mattmcwru/MPCNC-Build/Printed_Parts/MPCNC_Harbor_Fright_Cutout_Tool_Mount/images/f7ad241b8bc4b4fceb94680d84f262ed_preview_featured.jpg

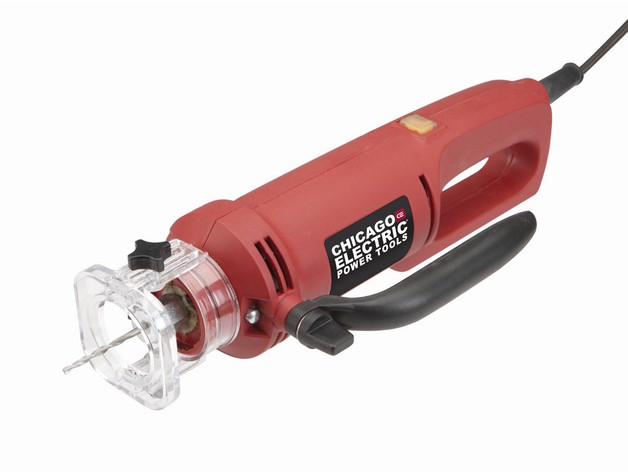
Printed_Parts/MPCNC_Harbor_Fright_Cutout_Tool_Mount/images/f7ad241b8bc4b4fceb94680d84f262ed_preview_featured.jpg
