mattmcwru/MPCNC-Build/Printed_Parts/MPCNC_Belt_Mount_Tensioner/images/5b18fd9a31a962e26c91805c583ef1f9_preview_featured.jpg

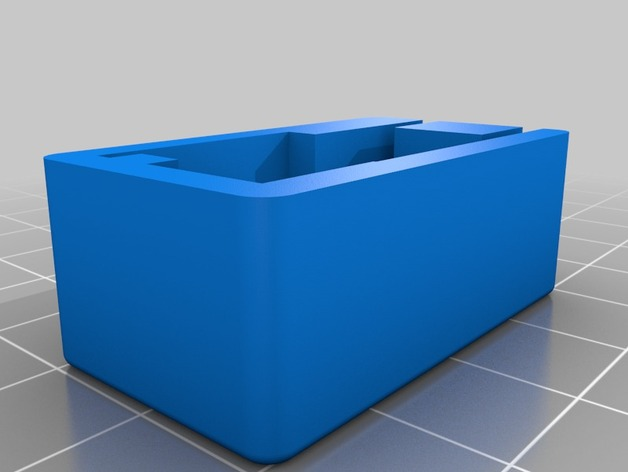
Printed_Parts/MPCNC_Belt_Mount_Tensioner/images/5b18fd9a31a962e26c91805c583ef1f9_preview_featured.jpg
