mattmcwru/MPCNC-Build/Printed_Parts/MPCNC_Belt_Mount_Tensioner/images/118bb4b1bc5640f76486a74081724c0c_preview_featured.jpg

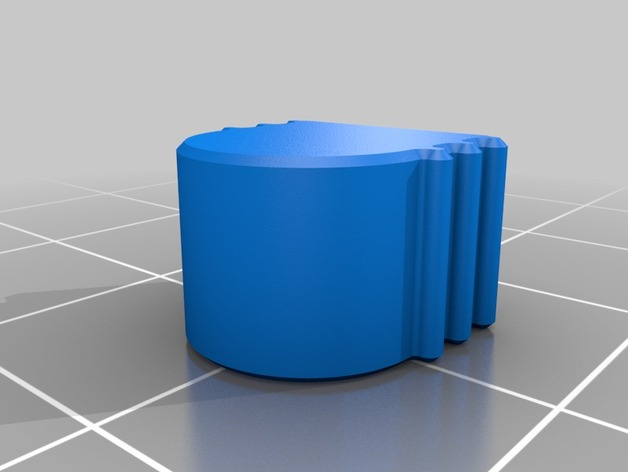
Printed_Parts/MPCNC_Belt_Mount_Tensioner/images/118bb4b1bc5640f76486a74081724c0c_preview_featured.jpg
