mattmcwru/MPCNC-Build/Printed_Parts/MPCNC_Belt_Mount_Tensioner/images/0129aa42869a3df930a46816420d5308_preview_featured.jpg

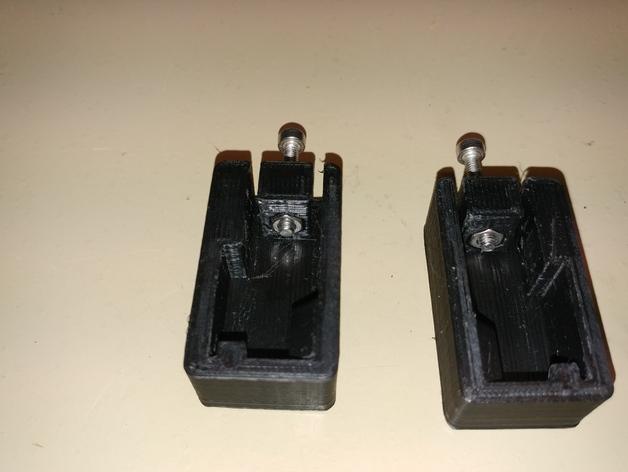
Printed_Parts/MPCNC_Belt_Mount_Tensioner/images/0129aa42869a3df930a46816420d5308_preview_featured.jpg
