mattmcwru/MPCNC-Build/Printed_Parts/MPCNC_Belt_Mount_Tensioner/images/a4fcf2e1120b8b7a6934baca6f5d6d2d_preview_featured.jpg

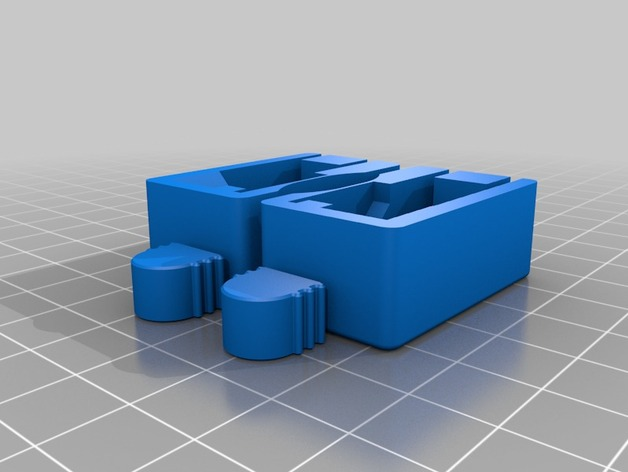
Printed_Parts/MPCNC_Belt_Mount_Tensioner/images/a4fcf2e1120b8b7a6934baca6f5d6d2d_preview_featured.jpg
