mattmcwru/MPCNC-Build/Printed_Parts/MPCNC_Belt_Mount_Tensioner/images/a68c1adb7a9085717290787e775d51c3_preview_featured.jpg

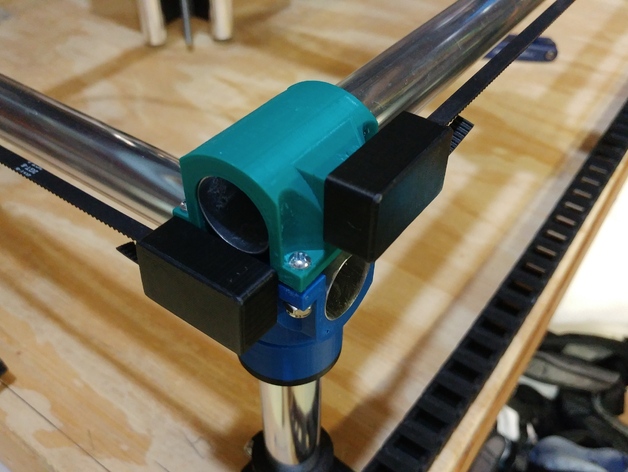
Printed_Parts/MPCNC_Belt_Mount_Tensioner/images/a68c1adb7a9085717290787e775d51c3_preview_featured.jpg
