mattmcwru/MPCNC-Build/Printed_Parts/MPCNC_Belt_Mount_Tensioner/images/b05523cd2e82c112d31e00afcdd35d0d_preview_featured.jpg

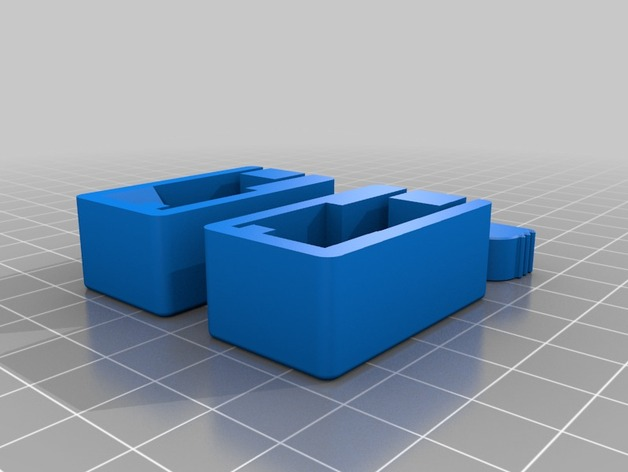
Printed_Parts/MPCNC_Belt_Mount_Tensioner/images/b05523cd2e82c112d31e00afcdd35d0d_preview_featured.jpg
