mattmcwru/MPCNC-Build/Printed_Parts/MPCNC_Belt_Mount_Tensioner/images/c8c6ffc99c06a0f2dce8c60c747f504d_preview_featured.jpg

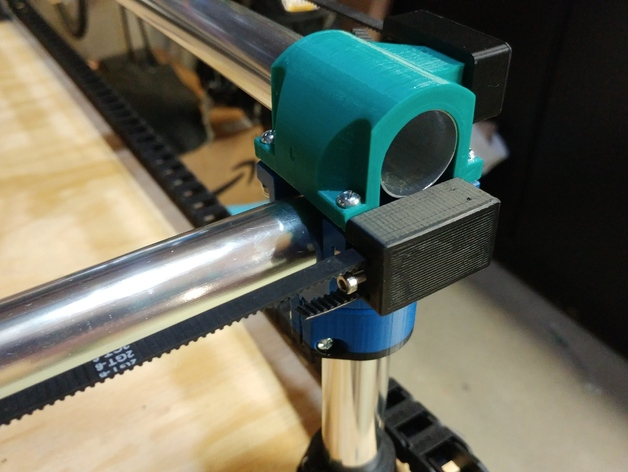
Printed_Parts/MPCNC_Belt_Mount_Tensioner/images/c8c6ffc99c06a0f2dce8c60c747f504d_preview_featured.jpg
