mattmcwru/MPCNC-Build/Printed_Parts/MPCNC_Belt_Mount_Tensioner/images/f6a336b1bc5efcc05f3e396646c9c925_preview_featured.jpg

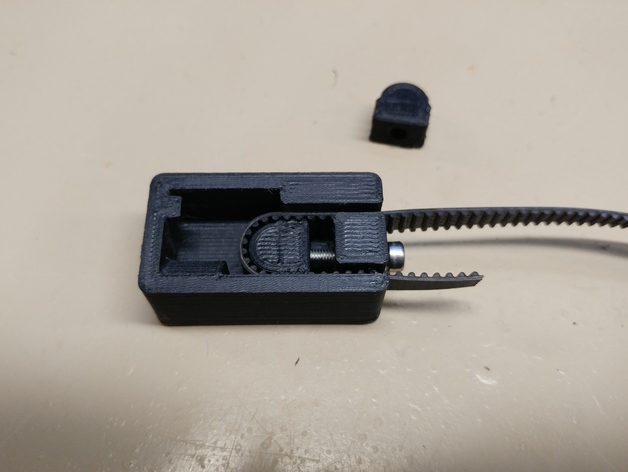
Printed_Parts/MPCNC_Belt_Mount_Tensioner/images/f6a336b1bc5efcc05f3e396646c9c925_preview_featured.jpg
