mattmcwru/MPCNC-Build/Printed_Parts/MPCNC_Dual_Endstop_Plates/images/4f32e94896d080e1614057bec8d3dcbc_preview_featured.jpg

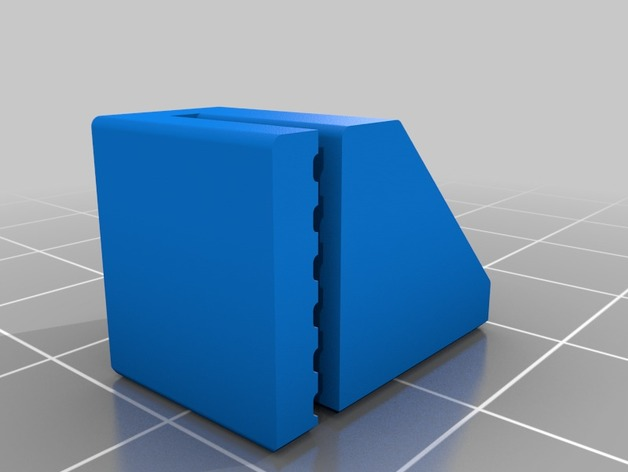
Printed_Parts/MPCNC_Dual_Endstop_Plates/images/4f32e94896d080e1614057bec8d3dcbc_preview_featured.jpg
