mattmcwru/MPCNC-Build/Printed_Parts/MPCNC_Dual_Endstop_Plates/images/6a49a4de091cbfa820c69511d2fc30e3_preview_featured.jpg

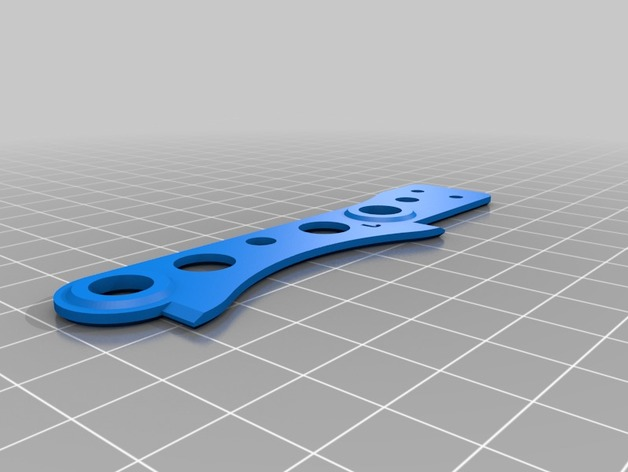
Printed_Parts/MPCNC_Dual_Endstop_Plates/images/6a49a4de091cbfa820c69511d2fc30e3_preview_featured.jpg
