mattmcwru/MPCNC-Build/Printed_Parts/MPCNC_Dual_Endstop_Plates/images/8cfda778197d712c990b11f8b45d0fdf_preview_featured.jpg

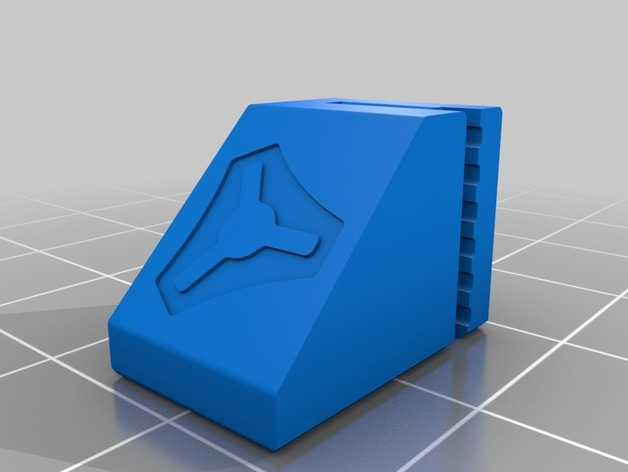
Printed_Parts/MPCNC_Dual_Endstop_Plates/images/8cfda778197d712c990b11f8b45d0fdf_preview_featured.jpg
