mattmcwru/MPCNC-Build/Printed_Parts/MPCNC_Dual_Endstop_Plates/images/de4bcbbb7ce7ebc580b4e3beed8e2b2a_preview_featured.jpg

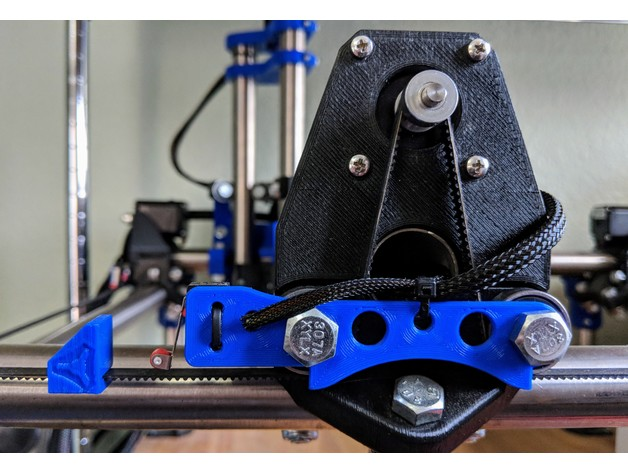
Printed_Parts/MPCNC_Dual_Endstop_Plates/images/de4bcbbb7ce7ebc580b4e3beed8e2b2a_preview_featured.jpg
