mattmcwru/MPCNC-Build/Printed_Parts/MPCNC_Harbor_Fright_Cutout_Tool_Mount/images/6a102007f02f2ae56196f1c2347e11f0_preview_featured.jpg

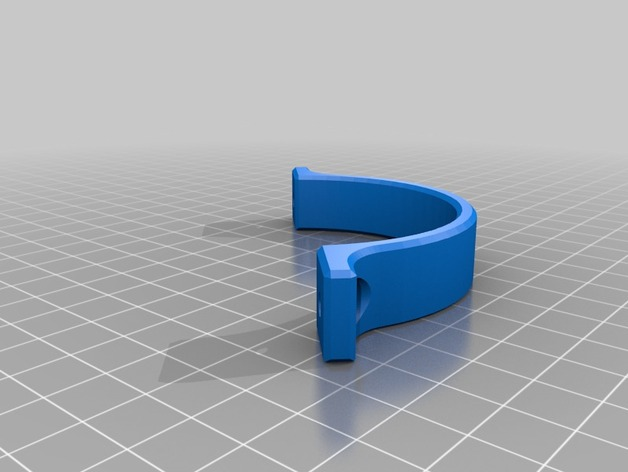
Printed_Parts/MPCNC_Harbor_Fright_Cutout_Tool_Mount/images/6a102007f02f2ae56196f1c2347e11f0_preview_featured.jpg
