mattmcwru/MPCNC-Build/Printed_Parts/MPCNC_Harbor_Fright_Cutout_Tool_Mount/images/9f360c5ab7736510df54c882e9dbf188_preview_featured.jpeg

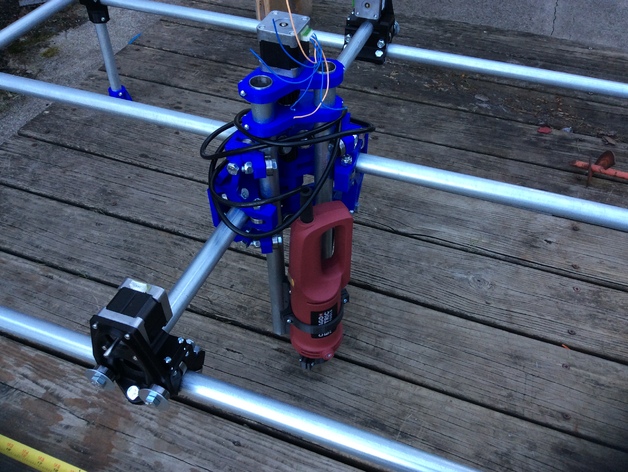
Printed_Parts/MPCNC_Harbor_Fright_Cutout_Tool_Mount/images/9f360c5ab7736510df54c882e9dbf188_preview_featured.jpeg
