mattmcwru/MPCNC-Build/Printed_Parts/MPCNC_Harbor_Fright_Cutout_Tool_Mount/images/031cdfd2edde983c23e4769dfbf6b3be_preview_featured.jpg

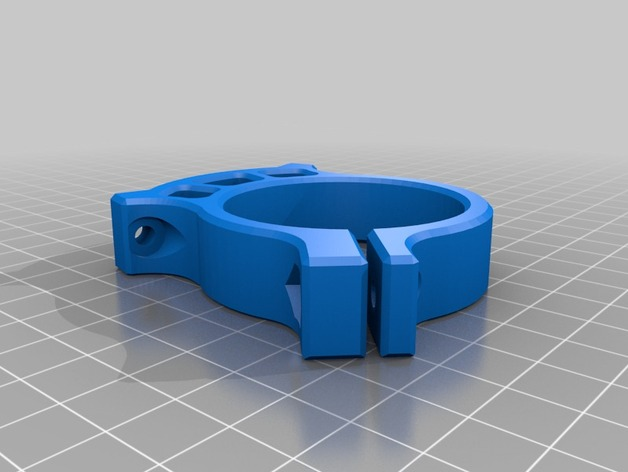
Printed_Parts/MPCNC_Harbor_Fright_Cutout_Tool_Mount/images/031cdfd2edde983c23e4769dfbf6b3be_preview_featured.jpg
