mattmcwru/MPCNC-Build/Printed_Parts/MPCNC_Harbor_Fright_Cutout_Tool_Mount/images/af0f49f9789b260aa54c982aef7ff063_preview_featured.jpg

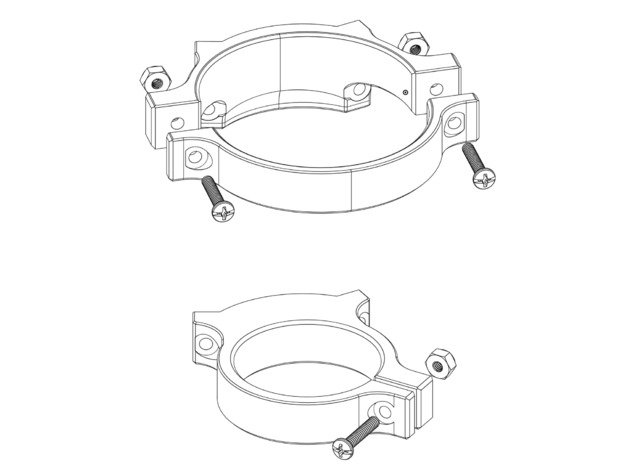
Printed_Parts/MPCNC_Harbor_Fright_Cutout_Tool_Mount/images/af0f49f9789b260aa54c982aef7ff063_preview_featured.jpg
