mattmcwru/MPCNC-Build/Printed_Parts/MPCNC_Harbor_Fright_Cutout_Tool_Mount/images/c593cc7923c47d9a5d14d5e01f252088_preview_featured.jpg

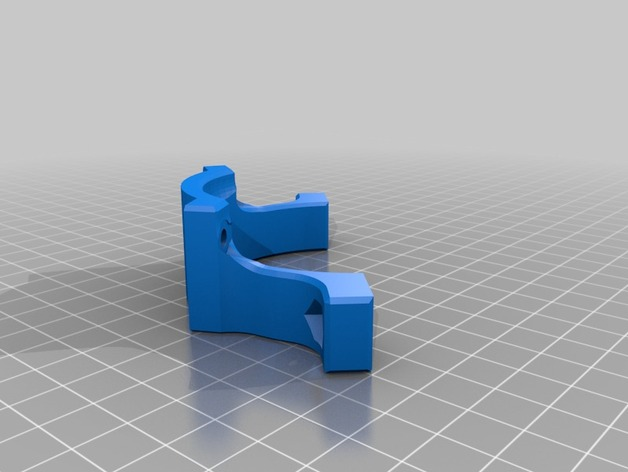
Printed_Parts/MPCNC_Harbor_Fright_Cutout_Tool_Mount/images/c593cc7923c47d9a5d14d5e01f252088_preview_featured.jpg
