mattmcwru/MPCNC-Build/Printed_Parts/MPCNC_Harbor_Fright_Cutout_Tool_Mount/images/d2b5ca33bd970f64a6301fa75ae2eb22_preview_featured.jpg

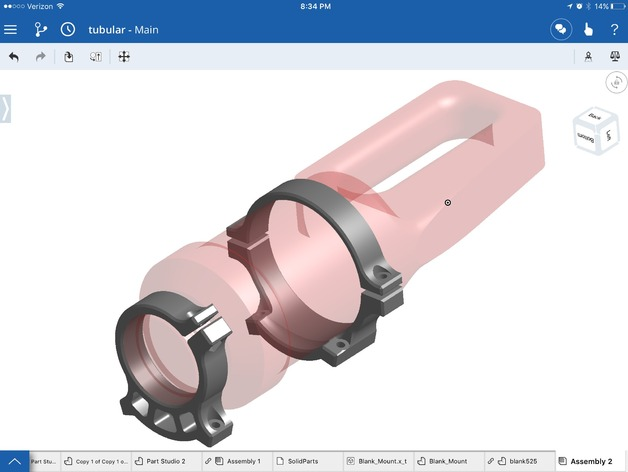
Printed_Parts/MPCNC_Harbor_Fright_Cutout_Tool_Mount/images/d2b5ca33bd970f64a6301fa75ae2eb22_preview_featured.jpg
