mattmcwru/MPCNC-Build/Printed_Parts/MPCNC_Pen_Holder/images/3a7e917523091c81a72ba8f813cce41a_preview_featured.jpg

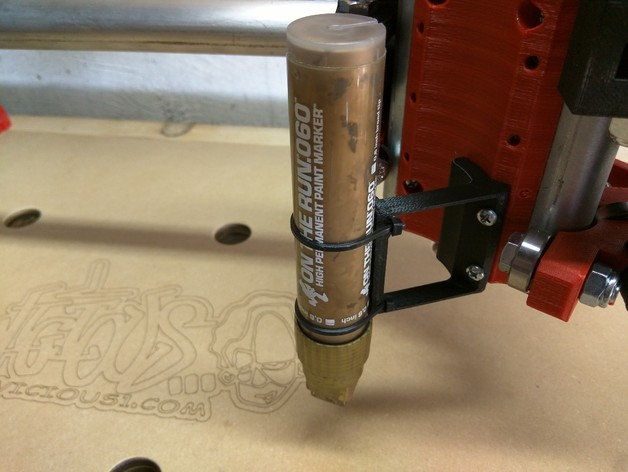
Printed_Parts/MPCNC_Pen_Holder/images/3a7e917523091c81a72ba8f813cce41a_preview_featured.jpg
