mattmcwru/MPCNC-Build/Printed_Parts/MPCNC_Pen_Holder/images/4c0c8f3b025ac8f8c0729633aa5849b6_preview_featured.jpg

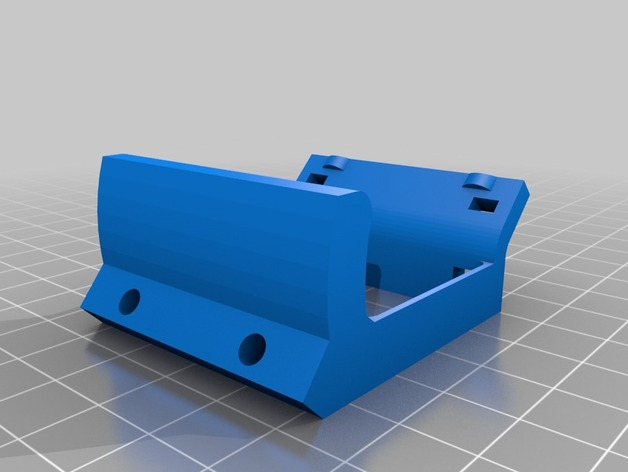
Printed_Parts/MPCNC_Pen_Holder/images/4c0c8f3b025ac8f8c0729633aa5849b6_preview_featured.jpg
