mattmcwru/MPCNC-Build/Printed_Parts/MPCNC_Pen_Holder/images/76b8588e2262610db6ddbcaa5a4f088d_preview_featured.jpg

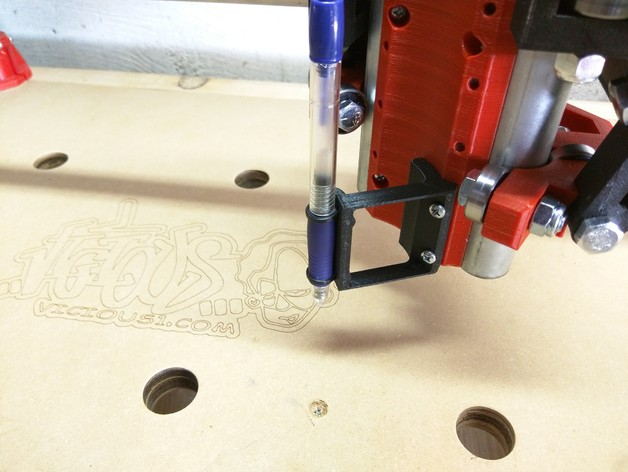
Printed_Parts/MPCNC_Pen_Holder/images/76b8588e2262610db6ddbcaa5a4f088d_preview_featured.jpg
