mattmcwru/MPCNC-Build/Printed_Parts/MPCNC_Pen_Holder/images/da3b15e401a95bbbfccdcf46860e9864_preview_featured.jpg

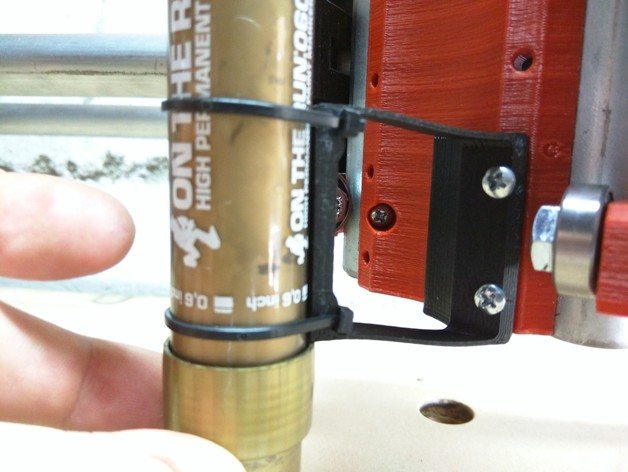
Printed_Parts/MPCNC_Pen_Holder/images/da3b15e401a95bbbfccdcf46860e9864_preview_featured.jpg
