mattmcwru/MPCNC-Build/Printed_Parts/MPCNC_Pipe_Caps/MPCNC_Pipe_Caps v2.png

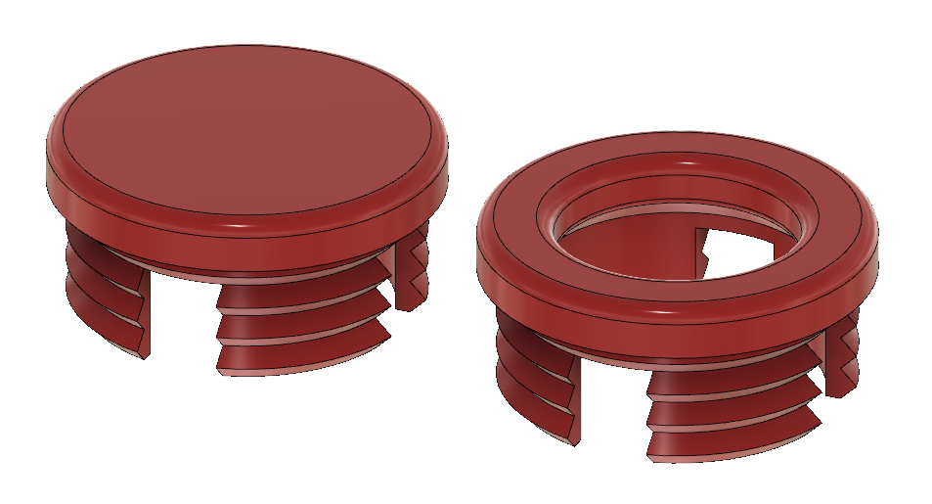
Printed_Parts/MPCNC_Pipe_Caps/MPCNC_Pipe_Caps v2.png
