mattmcwru/MPCNC-Build/Printed_Parts/MPCNC_TapeWireGuide/umc_projects/UM2_TapeWireGuideZMount_v3.3mf

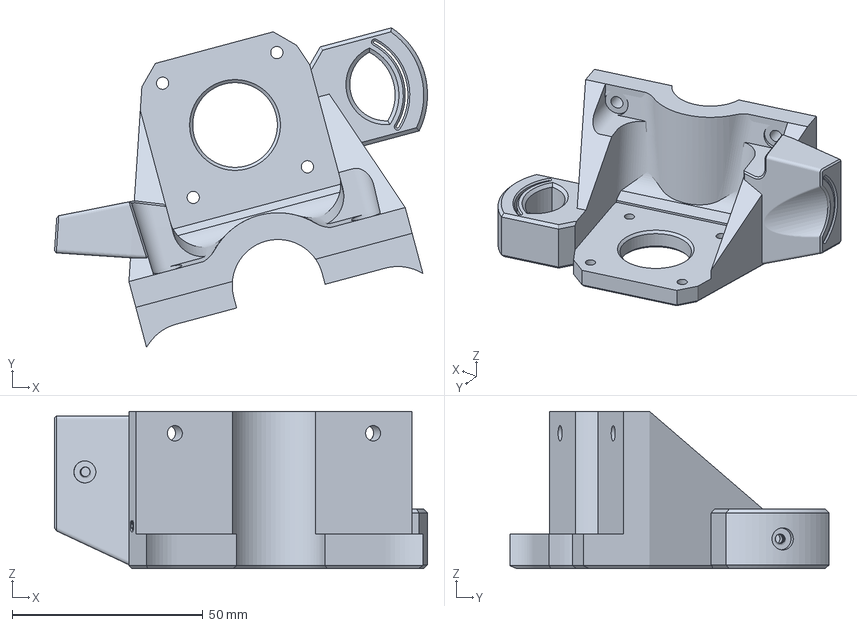
[picture p40: CAD file, 2019-02-07]
Printed_Parts/MPCNC_TapeWireGuide/umc_projects/UM2_TapeWireGuideZMount_v3.3mf
97.8 x 83.7 x 41.2 mm
