mattmcwru/MPCNC-Build/Printed_Parts/MPCNC_Belt_Mount_Tensioner/files/Belt_Anchor_Block_v2.1.stl

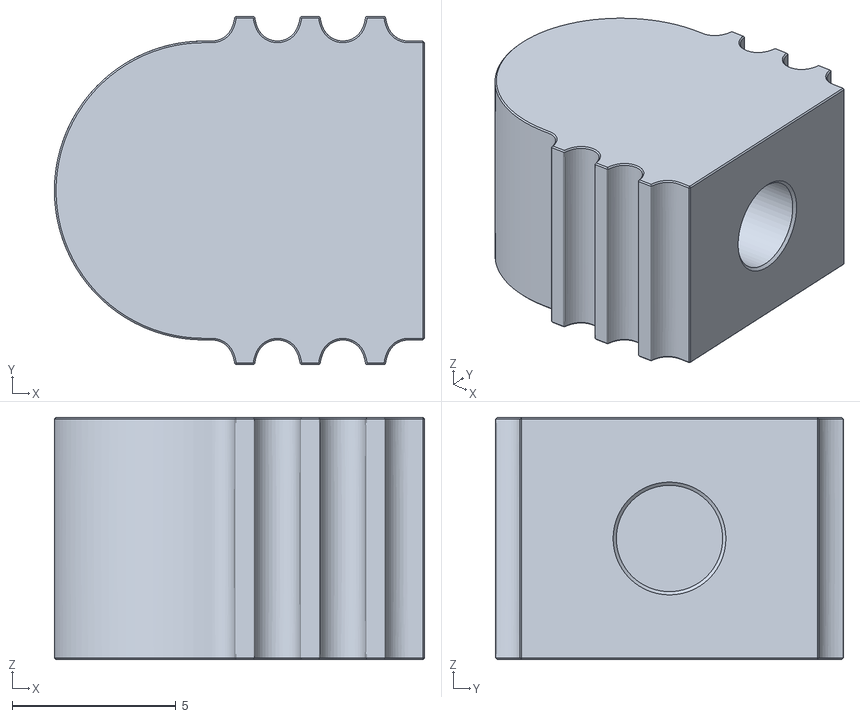
[picture p41: CAD file, 2019-02-19]
Printed_Parts/MPCNC_Belt_Mount_Tensioner/files/Belt_Anchor_Block_v2.1.stl
11.3 x 10.6 x 7.40
