mattmcwru/MPCNC-Build/Printed_Parts/MPCNC_Belt_Mount_Tensioner/umc_projects/UM2_Belt_Anchor_Block_v2.1.3mf

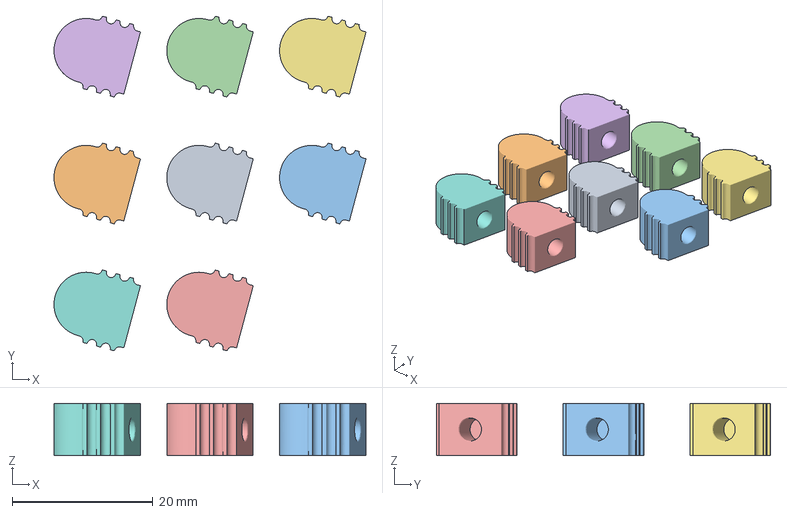
[picture p42: CAD file, 2019-02-19]
Printed_Parts/MPCNC_Belt_Mount_Tensioner/umc_projects/UM2_Belt_Anchor_Block_v2.1.3mf
44.3 x 47.5 x 7.40 mm
