mattmcwru/MPCNC-Build/Printed_Parts/MPCNC_BURLY_C_23p5/files/Lock-CornerC.STL

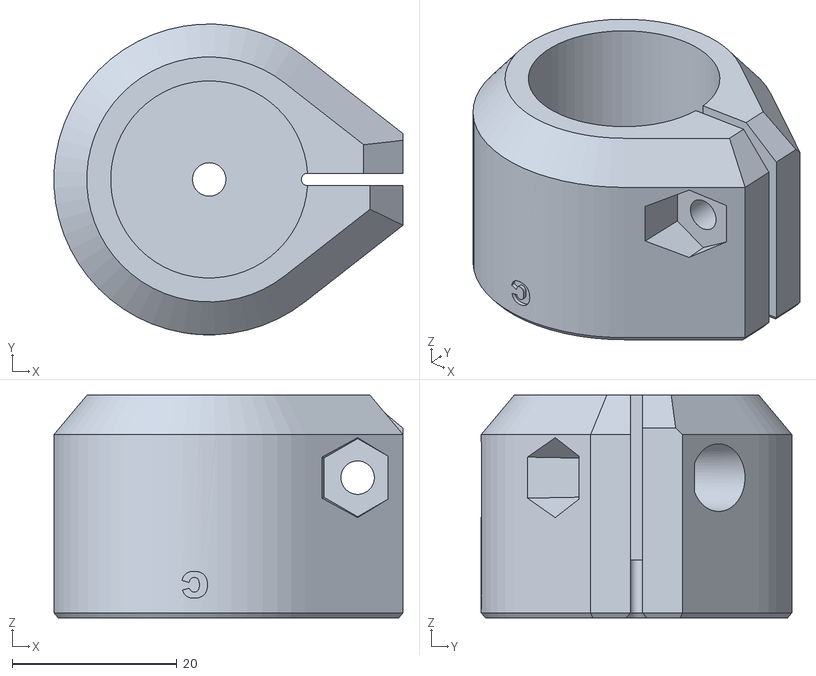
[picture p43: CAD file, 2019-01-15]
Printed_Parts/MPCNC_BURLY_C_23p5/files/Lock-CornerC.STL
42.3 x 37.7 x 27.0
