mattmcwru/MPCNC-Build/Printed_Parts/MPCNC_Dual_Endstop_Plates/files/Stop_Block.STL

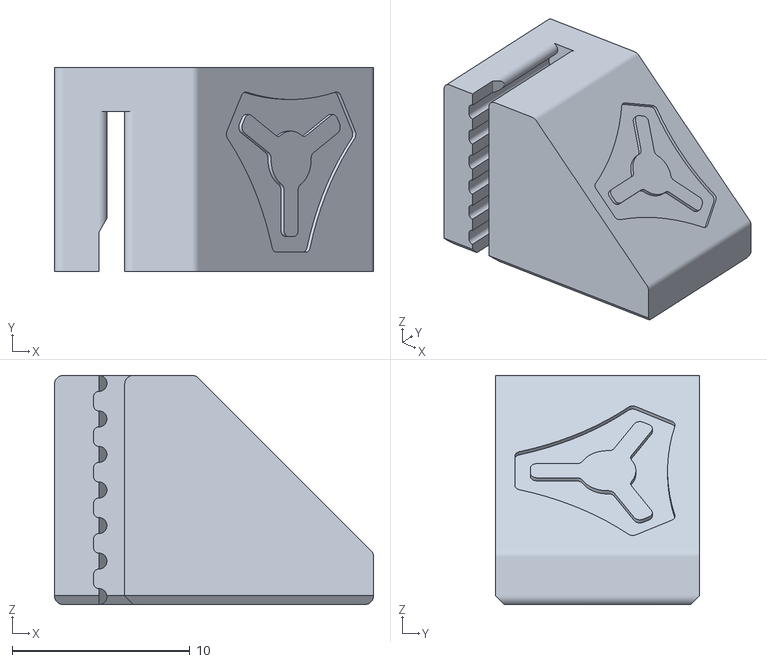
[picture p44: CAD file, 2019-01-26]
Printed_Parts/MPCNC_Dual_Endstop_Plates/files/Stop_Block.STL
17.9 x 11.5 x 12.9
