mattmcwru/MPCNC-Build/Printed_Parts/MPCNC_Dual_Endstop_Plates/umc_projects/UM2_C_Dual_Endstop_RollerPlateM_x2.3mf

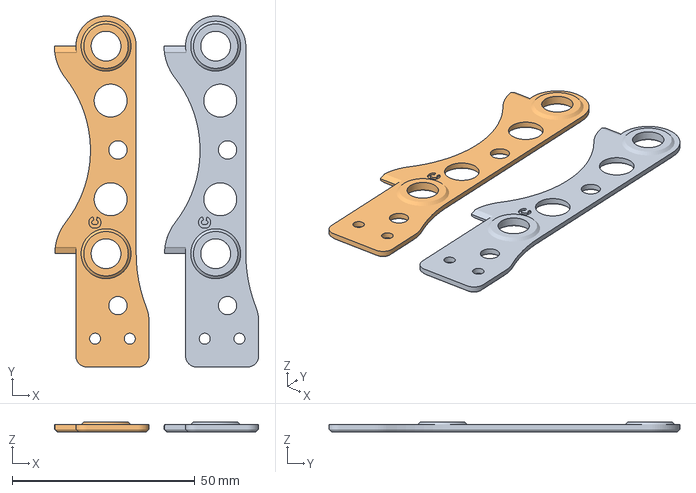
[picture p45: CAD file, 2019-01-29]
Printed_Parts/MPCNC_Dual_Endstop_Plates/umc_projects/UM2_C_Dual_Endstop_RollerPlateM_x2.3mf
55.9 x 96.0 x 2.75 mm
