mattmcwru/MPCNC-Build/Printed_Parts/MPCNC_Harbor_Fright_Cutout_Tool_Mount/files/hf_tool_mount_top.stl

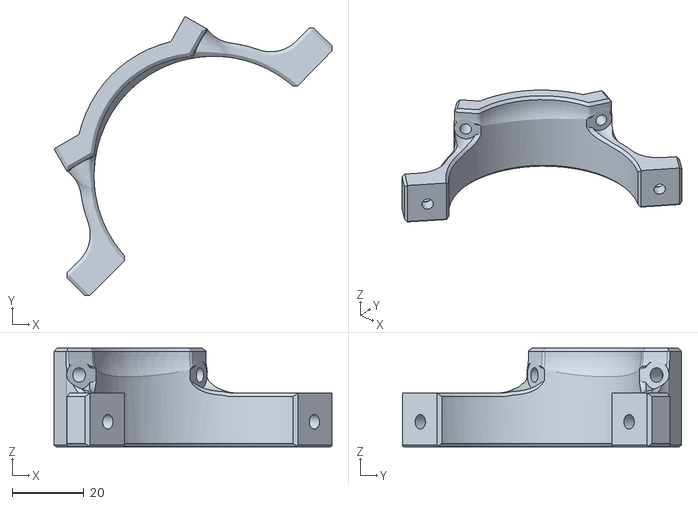
[picture p46: CAD file, 2019-01-15]
Printed_Parts/MPCNC_Harbor_Fright_Cutout_Tool_Mount/files/hf_tool_mount_top.stl
77.3 x 77.5 x 27.5
