mattmcwru/MPCNC-Build/Printed_Parts/MPCNC_Harbor_Fright_Cutout_Tool_Mount/umc-projects/UM2_hf_tool_mount_bottom.3mf

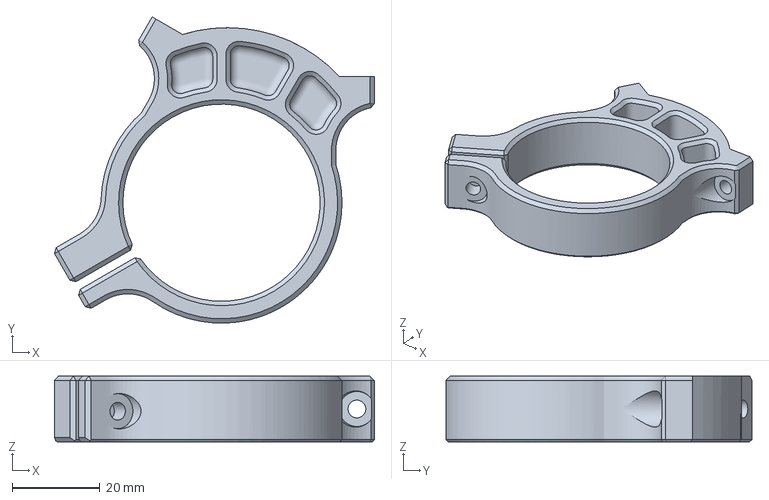
[picture p47: CAD file, 2019-01-15]
Printed_Parts/MPCNC_Harbor_Fright_Cutout_Tool_Mount/umc-projects/UM2_hf_tool_mount_bottom.3mf
73.1 x 69.9 x 15.0 mm
