mattmcwru/MPCNC-Build/Printed_Parts/MPCNC_Pipe_Caps/files/Cap_Open.stl

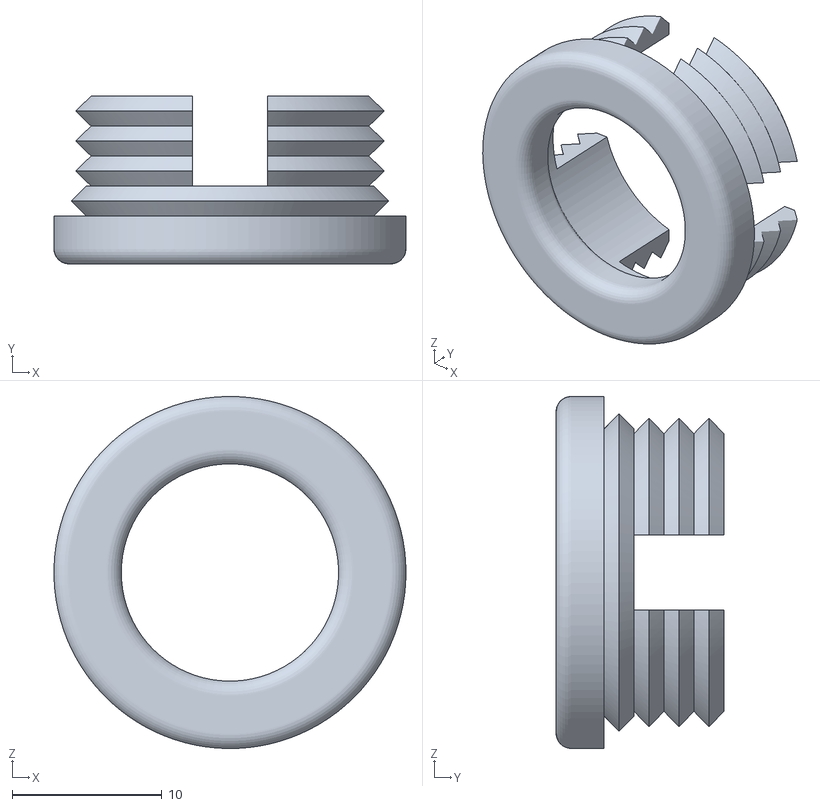
[picture p48: CAD file, 2019-01-27]
Printed_Parts/MPCNC_Pipe_Caps/files/Cap_Open.stl
23.5 x 11.2 x 23.5
