mattmcwru/MPCNC-Build/Printed_Parts/MPCNC_Pipe_Caps/umc_projects/UM2_Caps_6closed_3open.3mf

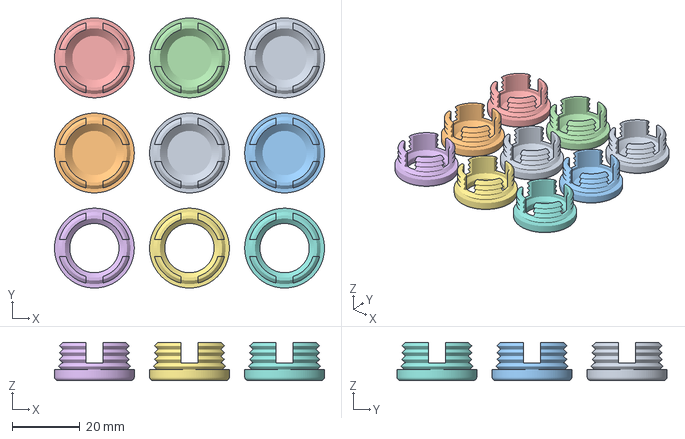
[picture p49: CAD file, 2019-01-29]
Printed_Parts/MPCNC_Pipe_Caps/umc_projects/UM2_Caps_6closed_3open.3mf
79.5 x 79.5 x 11.2 mm
