mattmcwru/MPCNC-Build/Printed_Parts/MPCNC_TapeWireGuide/files/TapeWireGuideMount_v10.stl

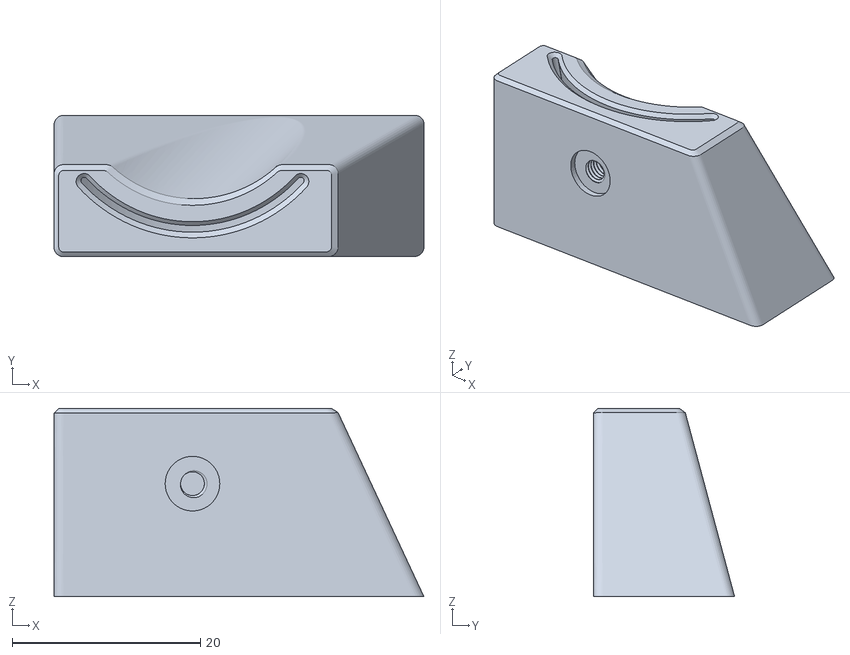
[picture p50: CAD file, 2019-02-05]
Printed_Parts/MPCNC_TapeWireGuide/files/TapeWireGuideMount_v10.stl
39.3 x 15.0 x 20.0
