mattmcwru/MPCNC-Build/Printed_Parts/MPCNC_TapeWireGuide/umc_projects/UM2_TapeWireGuideMount_v10.3mf

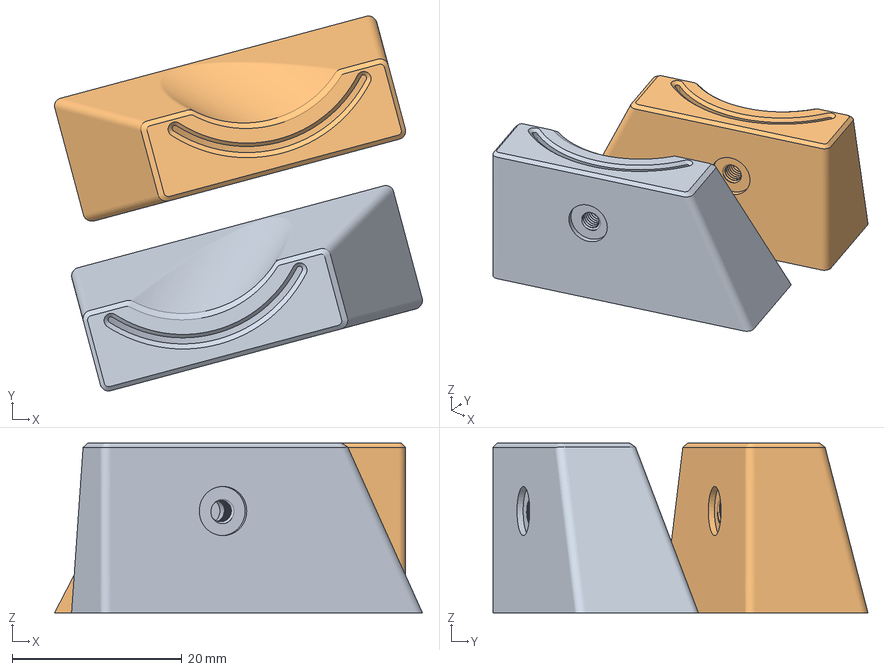
[picture p51: CAD file, 2019-02-05]
Printed_Parts/MPCNC_TapeWireGuide/umc_projects/UM2_TapeWireGuideMount_v10.3mf
43.4 x 44.2 x 20.0 mm
