mattmcwru/MPCNC-Build/Printed_Parts/MPCNC_Belt_Mount_Tensioner/files/belt_anchor_clip_set.stl

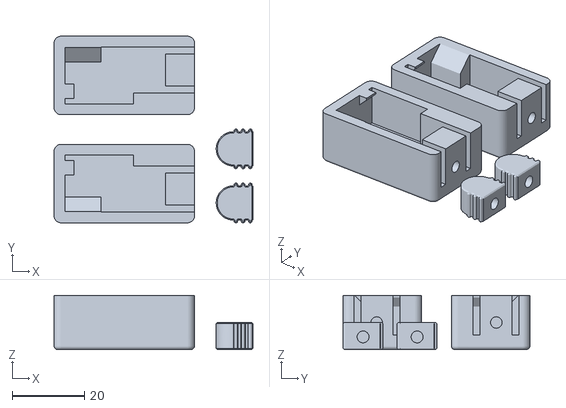
[picture p52: CAD file, 2019-01-24]
Printed_Parts/MPCNC_Belt_Mount_Tensioner/files/belt_anchor_clip_set.stl
55.2 x 51.8 x 15.0
