mattmcwru/MPCNC-Build/Printed_Parts/MPCNC_BURLY_C_23p5/files/C-RollerM.STL

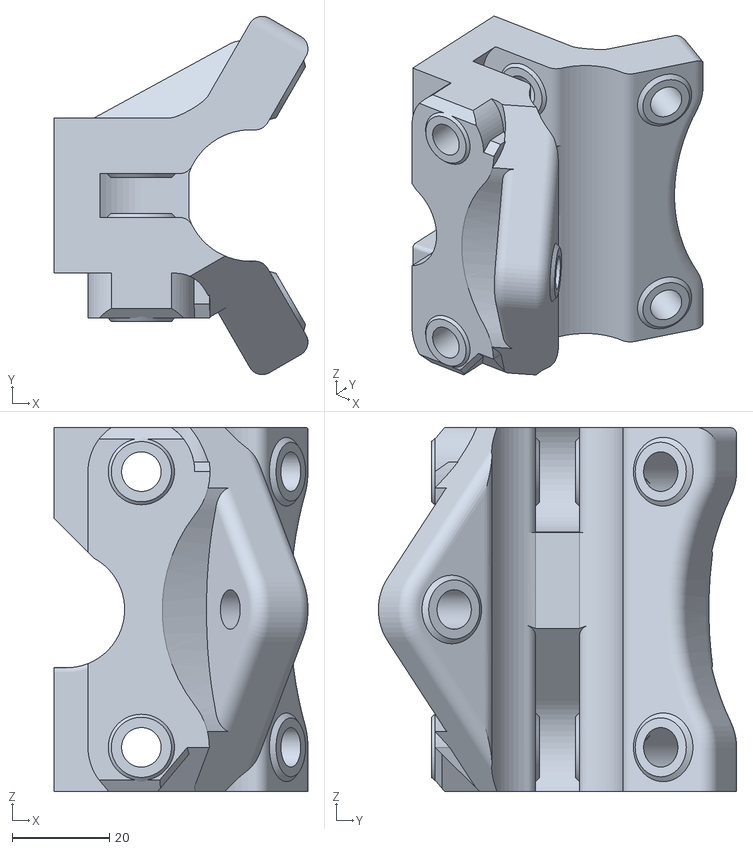
[picture p53: CAD file, 2019-01-15]
Printed_Parts/MPCNC_BURLY_C_23p5/files/C-RollerM.STL
52.3 x 73.8 x 75.0
