mattmcwru/MPCNC-Build/Printed_Parts/MPCNC_BURLY_C_23p5/umc-projects/UM2_XY_C_Burly.3mf

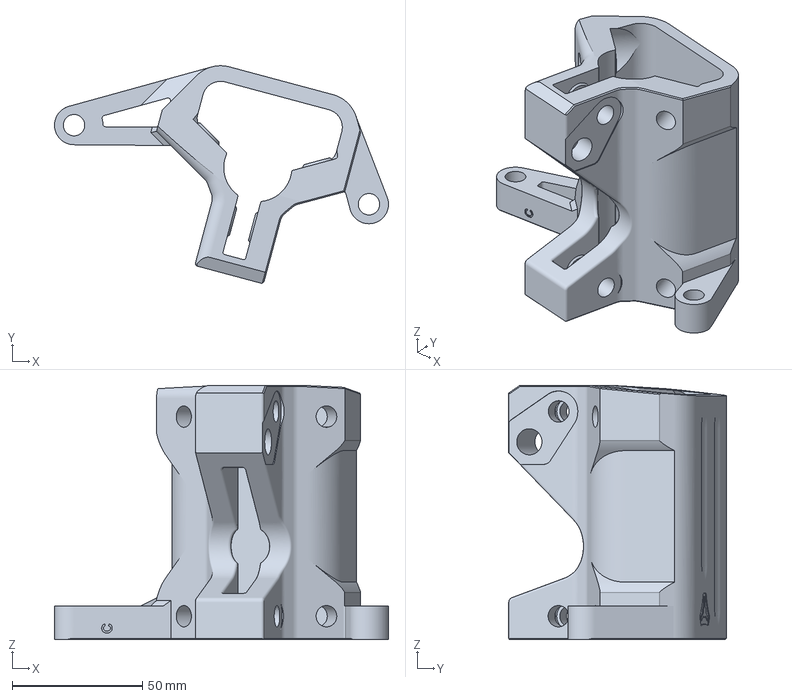
[picture p54: CAD file, 2019-01-24]
Printed_Parts/MPCNC_BURLY_C_23p5/umc-projects/UM2_XY_C_Burly.3mf
128.2 x 83.5 x 97.6 mm
