mattmcwru/MPCNC-Build/Printed_Parts/MPCNC_Dual_Endstop_Plates/umc_projects/UM2_Stop_Block_2each.3mf

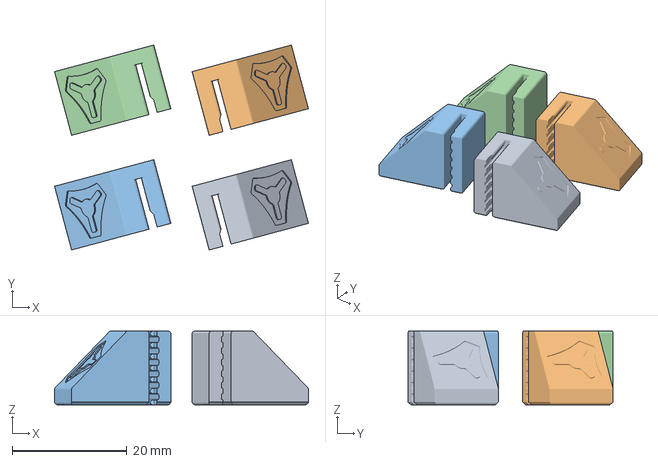
[picture p55: CAD file, 2019-01-26]
Printed_Parts/MPCNC_Dual_Endstop_Plates/umc_projects/UM2_Stop_Block_2each.3mf
44.3 x 35.8 x 12.9 mm
