mattmcwru/MPCNC-Build/Printed_Parts/MPCNC_Harbor_Fright_Cutout_Tool_Mount/files/hf_tool_mount_bottom.stl

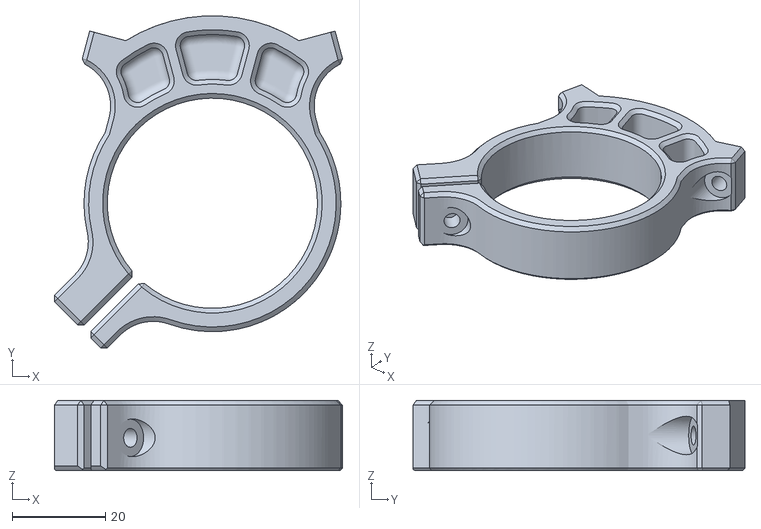
[picture p56: CAD file, 2019-01-15]
Printed_Parts/MPCNC_Harbor_Fright_Cutout_Tool_Mount/files/hf_tool_mount_bottom.stl
61.7 x 71.1 x 15.0
