mattmcwru/MPCNC-Build/Printed_Parts/MPCNC_Pipe_Caps/umc_projects/UM2_Caps_4open.3mf

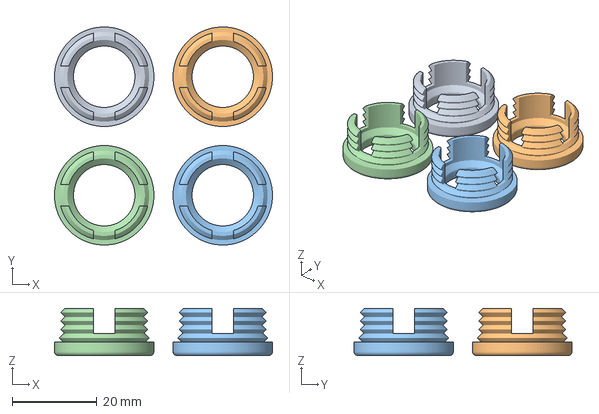
[picture p57: CAD file, 2019-01-29]
Printed_Parts/MPCNC_Pipe_Caps/umc_projects/UM2_Caps_4open.3mf
51.5 x 51.5 x 11.2 mm
