mattmcwru/MPCNC-Build/Printed_Parts/MPCNC_TapeWireGuide/files/TapeWireGuide_RollerMount_v2.stl

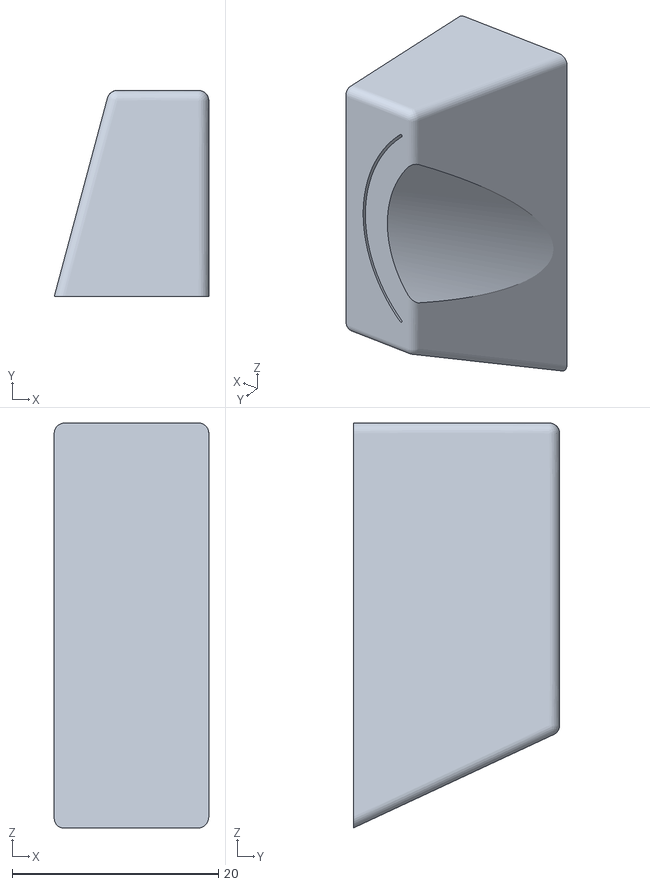
[picture p58: CAD file, 2019-02-04]
Printed_Parts/MPCNC_TapeWireGuide/files/TapeWireGuide_RollerMount_v2.stl
15.0 x 20.0 x 39.3
