mattmcwru/MPCNC-Build/Printed_Parts/MPCNC_Belt_Mount_Tensioner/files/belt_anchor_lower_clip_set.stl

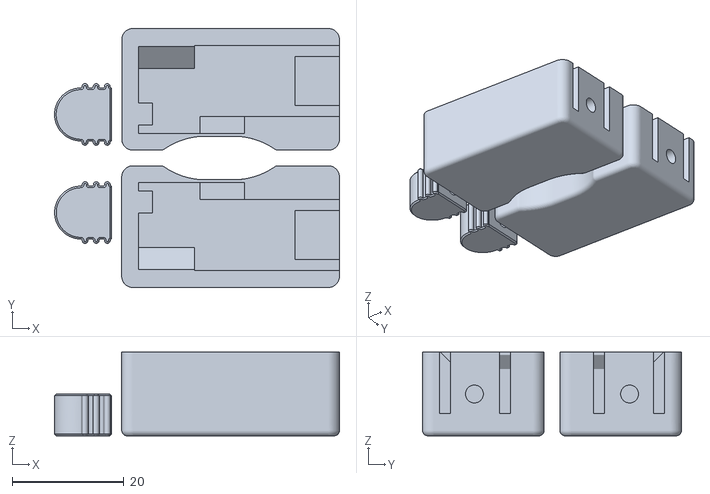
[picture p59: CAD file, 2019-01-24]
Printed_Parts/MPCNC_Belt_Mount_Tensioner/files/belt_anchor_lower_clip_set.stl
51.1 x 46.4 x 15.0
