mattmcwru/MPCNC-Build/Printed_Parts/MPCNC_BURLY_C_23p5/umc-projects/UM2_C-RollerMount_x2.3mf

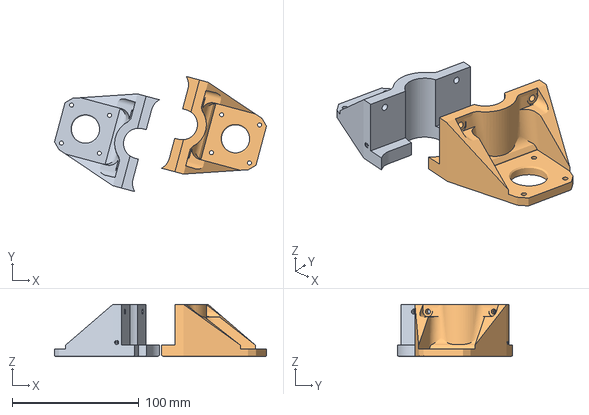
[picture p60: CAD file, 2019-01-18]
Printed_Parts/MPCNC_BURLY_C_23p5/umc-projects/UM2_C-RollerMount_x2.3mf
167.2 x 90.9 x 41.2 mm
