mattmcwru/MPCNC-Build/Printed_Parts/MPCNC_Belt_Mount_Tensioner/files/belt_anchor_lower.stl

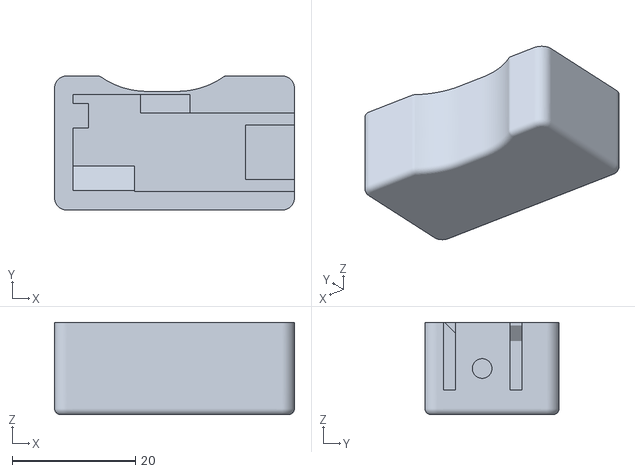
[picture p61: CAD file, 2019-01-24]
Printed_Parts/MPCNC_Belt_Mount_Tensioner/files/belt_anchor_lower.stl
39.0 x 21.8 x 15.0
