mattmcwru/MPCNC-Build/Printed_Parts/MPCNC_Belt_Mount_Tensioner/umc_projects/UM2_belt_anchor_2each.3mf

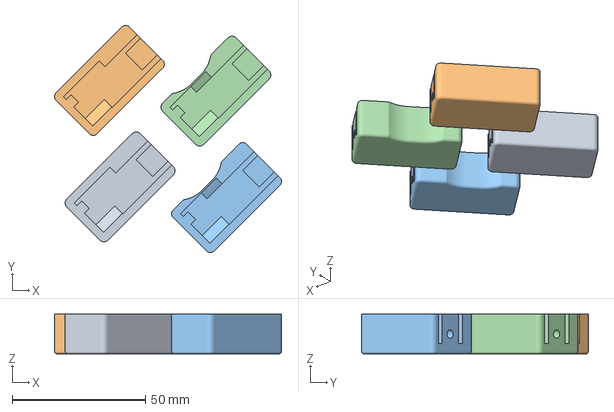
[picture p62: CAD file, 2019-01-24]
Printed_Parts/MPCNC_Belt_Mount_Tensioner/umc_projects/UM2_belt_anchor_2each.3mf
85.3 x 85.3 x 15.0 mm
