mattmcwru/MPCNC-Build/Printed_Parts/MPCNC_BURLY_C_23p5/files/C-Foot_2018.STL

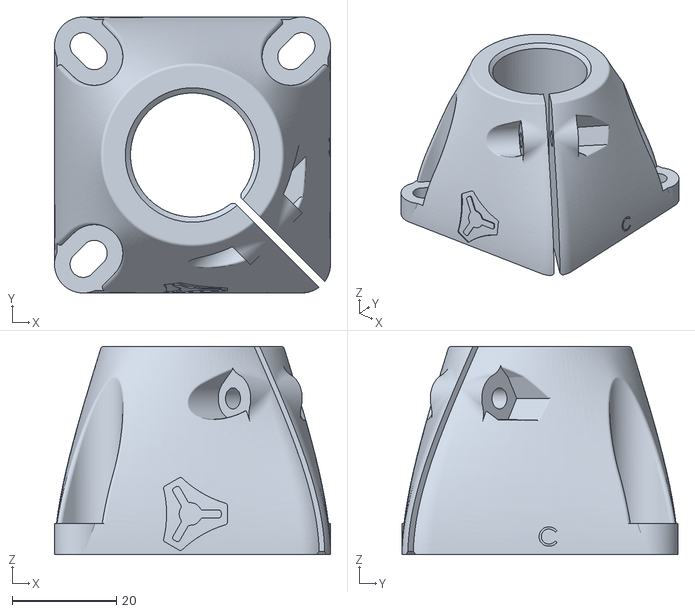
[picture p63: CAD file, 2019-01-15]
Printed_Parts/MPCNC_BURLY_C_23p5/files/C-Foot_2018.STL
53.0 x 53.0 x 40.0
