mattmcwru/MPCNC-Build/Printed_Parts/MPCNC_BURLY_C_23p5/umc-projects/UM2_Z_Motor_XYZ_C_Burly.3mf

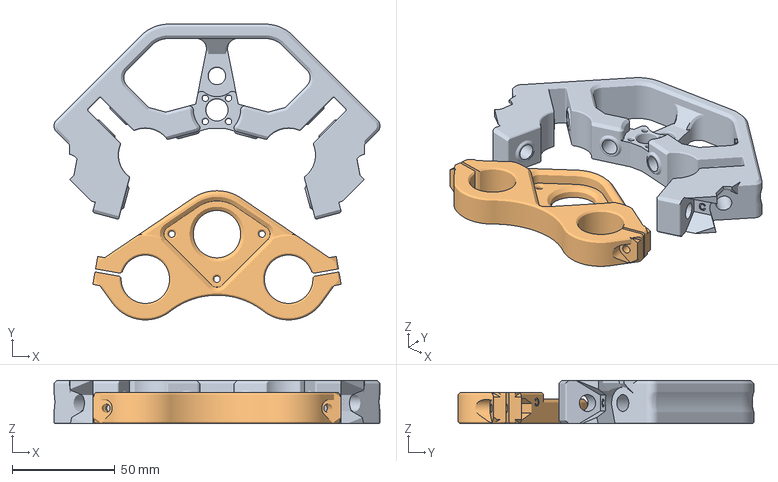
[picture p64: CAD file, 2019-01-18]
Printed_Parts/MPCNC_BURLY_C_23p5/umc-projects/UM2_Z_Motor_XYZ_C_Burly.3mf
158.4 x 143.7 x 21.0 mm
