mattmcwru/MPCNC-Build/Printed_Parts/MPCNC_Belt_Mount_Tensioner/files/belt_clip.stl

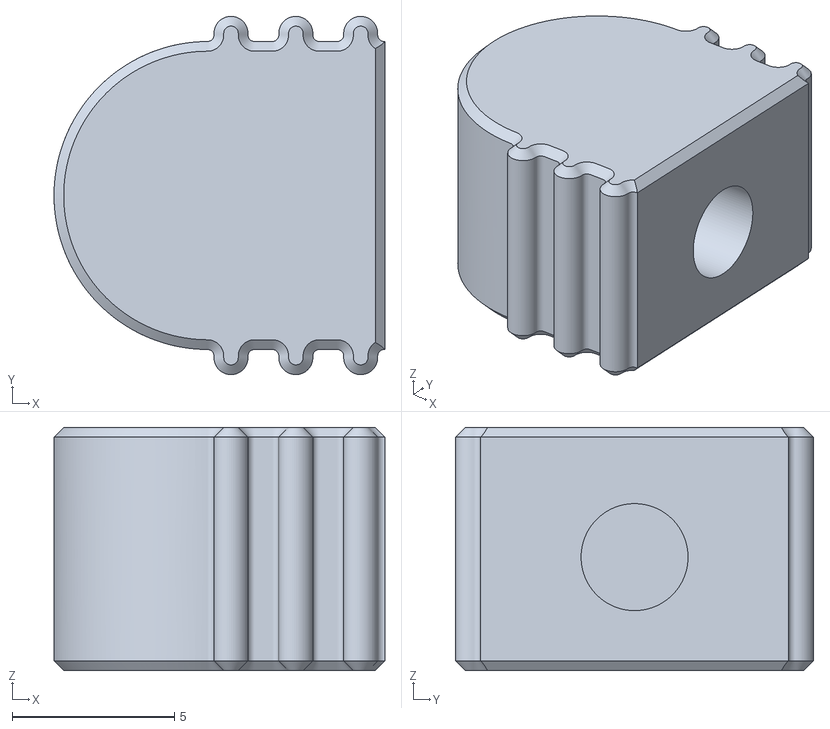
[picture p65: CAD file, 2019-01-24]
Printed_Parts/MPCNC_Belt_Mount_Tensioner/files/belt_clip.stl
10.2 x 11.1 x 7.50
