mattmcwru/MPCNC-Build/Printed_Parts/MPCNC_BURLY_C_23p5/files/BottomM_CornerC.STL

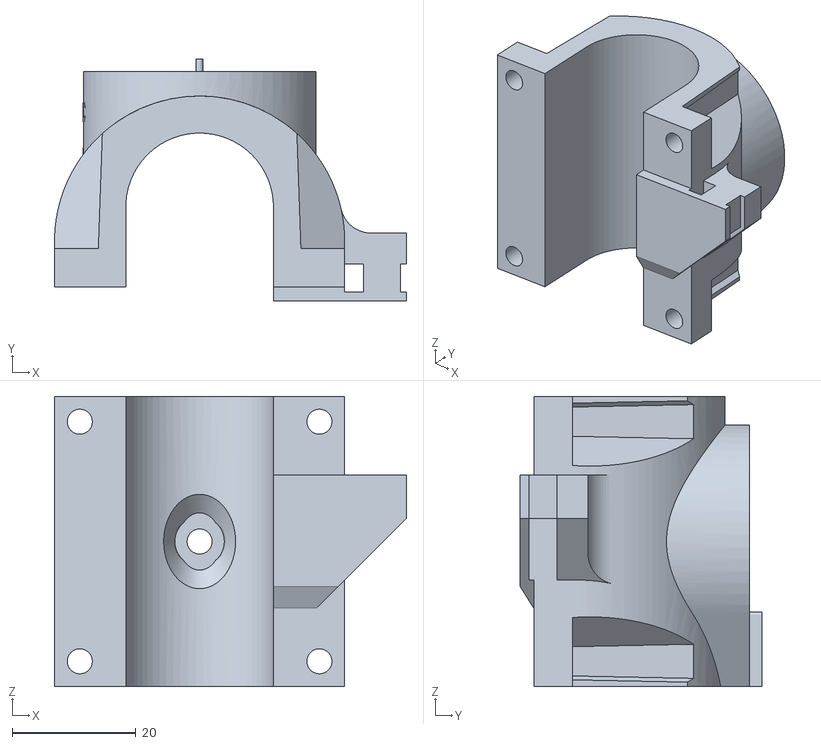
[picture p66: CAD file, 2019-01-15]
Printed_Parts/MPCNC_BURLY_C_23p5/files/BottomM_CornerC.STL
57.0 x 39.2 x 47.0
