mattmcwru/MPCNC-Build/Printed_Parts/MPCNC_BURLY_C_23p5/umc-projects/UM2_Z_Lower_Motor.3mf

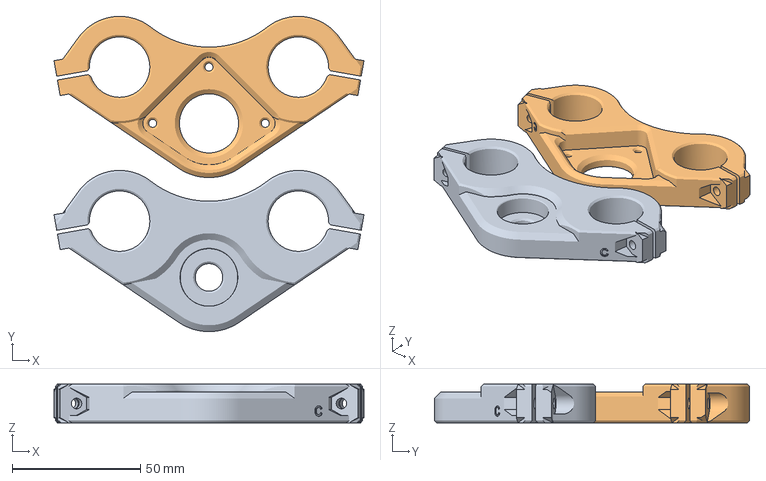
[picture p67: CAD file, 2019-01-18]
Printed_Parts/MPCNC_BURLY_C_23p5/umc-projects/UM2_Z_Lower_Motor.3mf
120.7 x 122.8 x 15.0 mm
