mattmcwru/MPCNC-Build/Printed_Parts/MPCNC_Dual_Endstop_Plates/files/C_Dual_RollerPlate.STL

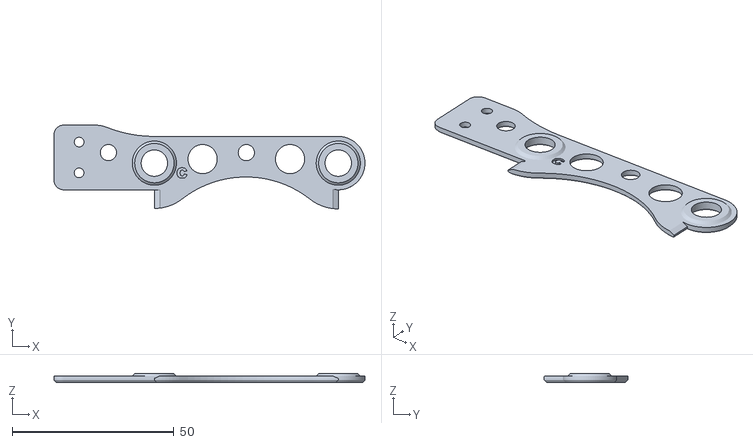
[picture p68: CAD file, 2019-01-26]
Printed_Parts/MPCNC_Dual_Endstop_Plates/files/C_Dual_RollerPlate.STL
96.0 x 25.9 x 2.75
