mattmcwru/MPCNC-Build/Printed_Parts/MPCNC_BURLY_C_23p5/umc-projects/UM2_Gantry_Corner_Spacers.3mf

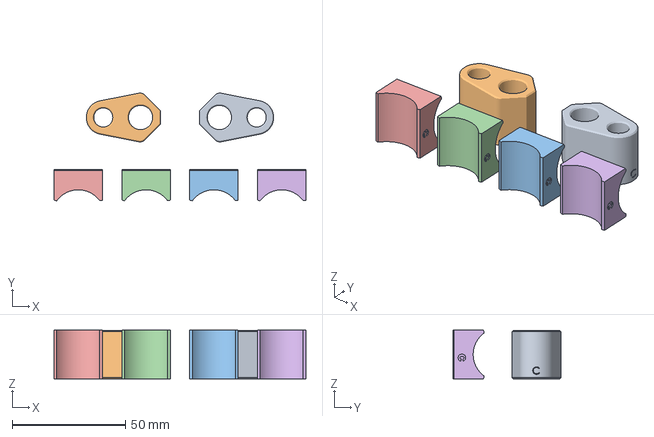
[picture p69: CAD file, 2019-01-18]
Printed_Parts/MPCNC_BURLY_C_23p5/umc-projects/UM2_Gantry_Corner_Spacers.3mf
111.5 x 47.7 x 21.5 mm
