mattmcwru/MPCNC-Build/Printed_Parts/MPCNC_BURLY_C_23p5/umc-projects/UM2_Top_CornerC_test.3mf

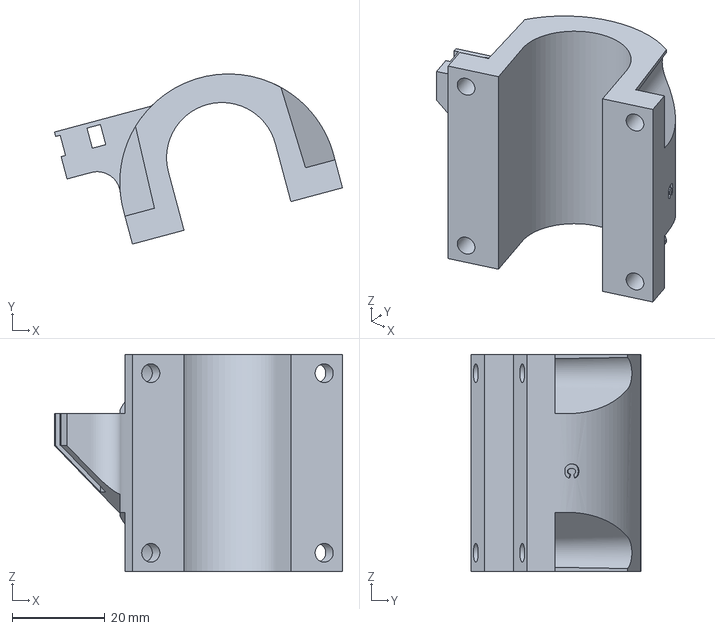
[picture p70: CAD file, 2019-01-18]
Printed_Parts/MPCNC_BURLY_C_23p5/umc-projects/UM2_Top_CornerC_test.3mf
62.2 x 36.8 x 47.0 mm
