mattmcwru/MPCNC-Build/Printed_Parts/MPCNC_TapeWireGuide/umc_projects/UM2_TapeWireGuideMount_v8_Mirror.3mf

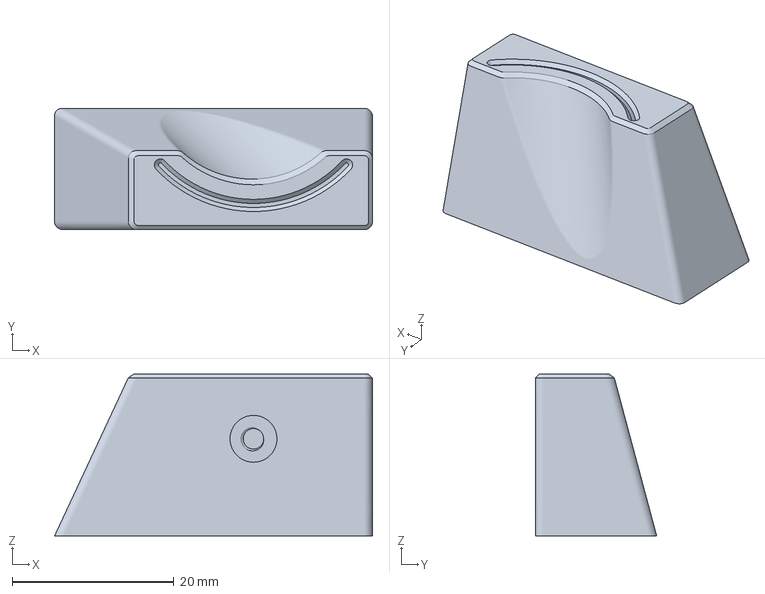
[picture p71: CAD file, 2019-02-04]
Printed_Parts/MPCNC_TapeWireGuide/umc_projects/UM2_TapeWireGuideMount_v8_Mirror.3mf
39.3 x 15.0 x 20.0 mm
