mattmcwru/MPCNC-Build/Printed_Parts/MPCNC_BURLY_C_23p5/files/C-RollerPlate.STL

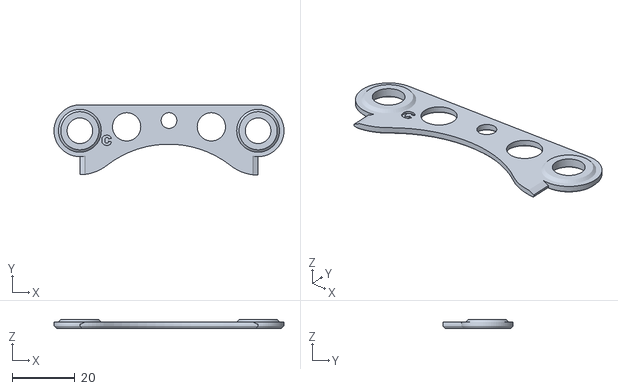
[picture p72: CAD file, 2019-01-15]
Printed_Parts/MPCNC_BURLY_C_23p5/files/C-RollerPlate.STL
73.3 x 22.4 x 2.75
