mattmcwru/MPCNC-Build/Printed_Parts/MPCNC_BURLY_C_23p5/umc-projects/UM2_C-RollerPlate_x4.3mf

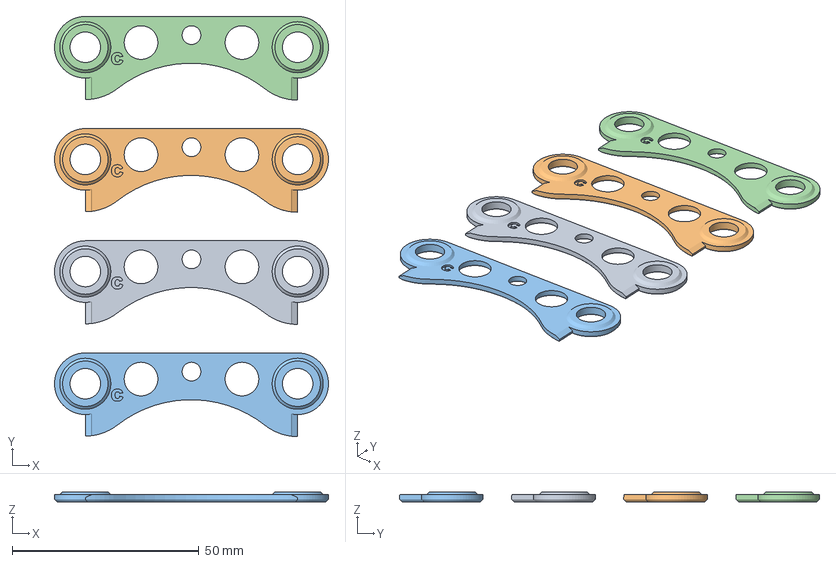
[picture p73: CAD file, 2019-01-18]
Printed_Parts/MPCNC_BURLY_C_23p5/umc-projects/UM2_C-RollerPlate_x4.3mf
73.3 x 112.4 x 2.75 mm
