mattmcwru/MPCNC-Build/Printed_Parts/MPCNC_BURLY_C_23p5/files/XYZ_C_Burly.STL

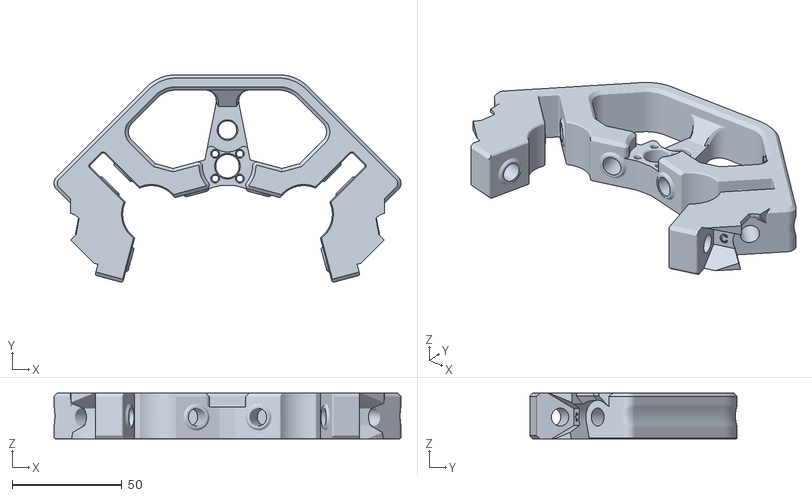
[picture p74: CAD file, 2019-01-15]
Printed_Parts/MPCNC_BURLY_C_23p5/files/XYZ_C_Burly.STL
158.4 x 94.7 x 21.0
