mattmcwru/MPCNC-Build/Printed_Parts/MPCNC_BURLY_C_23p5/umc-projects/UM2_C-Roller_1each.3mf

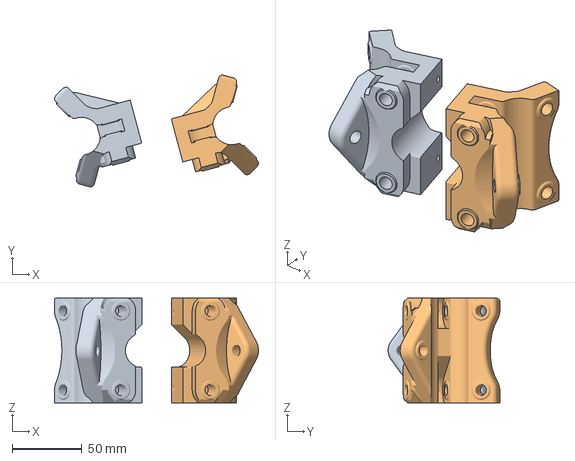
[picture p75: CAD file, 2019-01-18]
Printed_Parts/MPCNC_BURLY_C_23p5/umc-projects/UM2_C-Roller_1each.3mf
146.4 x 80.2 x 75.0 mm
