mattmcwru/MPCNC-Build/Printed_Parts/MPCNC_TapeWireGuide/files/TapeWireGuideTower_v2.stl

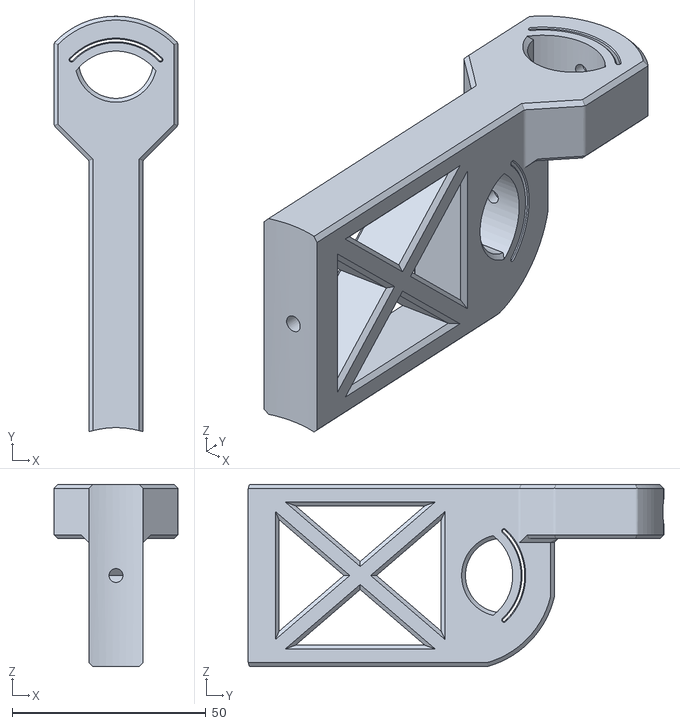
[picture p76: CAD file, 2019-02-04]
Printed_Parts/MPCNC_TapeWireGuide/files/TapeWireGuideTower_v2.stl
32.0 x 107.3 x 47.0
