mattmcwru/MPCNC-Build/Printed_Parts/MPCNC_BURLY_C_23p5/files/Top_CornerC.STL

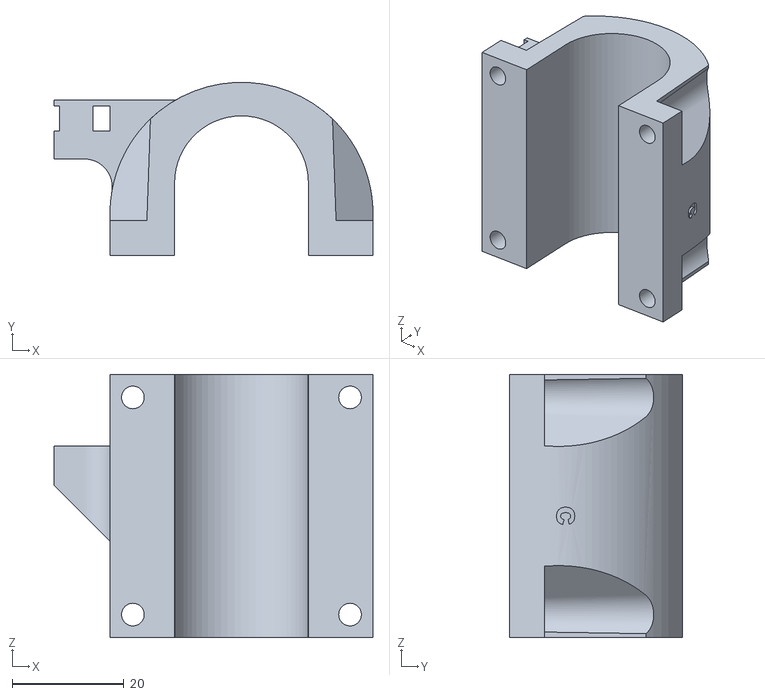
[picture p77: CAD file, 2019-01-15]
Printed_Parts/MPCNC_BURLY_C_23p5/files/Top_CornerC.STL
57.0 x 30.9 x 47.0
