mattmcwru/MPCNC-Build/Printed_Parts/MPCNC_BURLY_C_23p5/umc-projects/UM2_TopM_CornerC.3mf

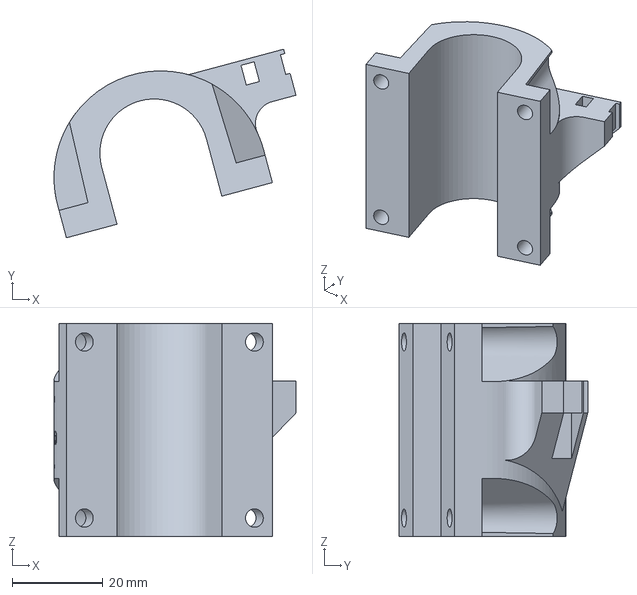
[picture p78: CAD file, 2019-01-18]
Printed_Parts/MPCNC_BURLY_C_23p5/umc-projects/UM2_TopM_CornerC.3mf
53.3 x 41.6 x 47.0 mm
