mattmcwru/MPCNC-Build/Printed_Parts/MPCNC_BURLY_C_23p5/files/Z_Motor_C_Burly.STL

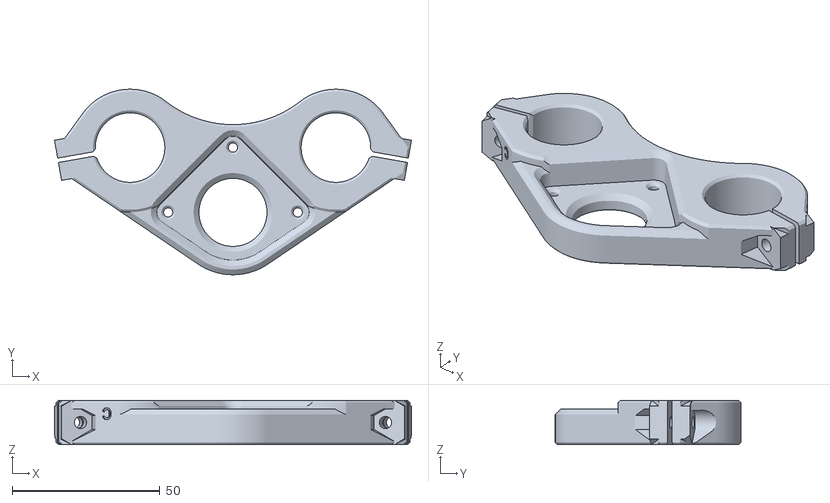
[picture p79: CAD file, 2019-01-15]
Printed_Parts/MPCNC_BURLY_C_23p5/files/Z_Motor_C_Burly.STL
120.7 x 62.8 x 15.0
