mattmcwru/MPCNC-Build/Printed_Parts/MPCNC_TapeWireGuide/umc_projects/UM2_TapeWireGuideTower_v2.3mf

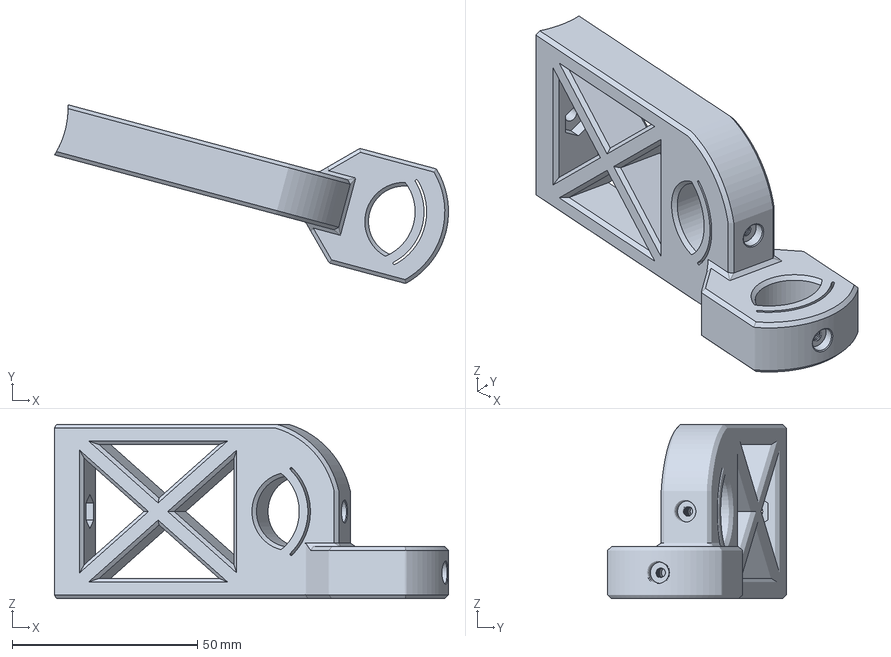
[picture p80: CAD file, 2019-02-04]
Printed_Parts/MPCNC_TapeWireGuide/umc_projects/UM2_TapeWireGuideTower_v2.3mf
106.2 x 48.1 x 47.0 mm
