mattmcwru/MPCNC-Build/Printed_Parts/MPCNC_BURLY_C_23p5/files/C-RollerMount.STL

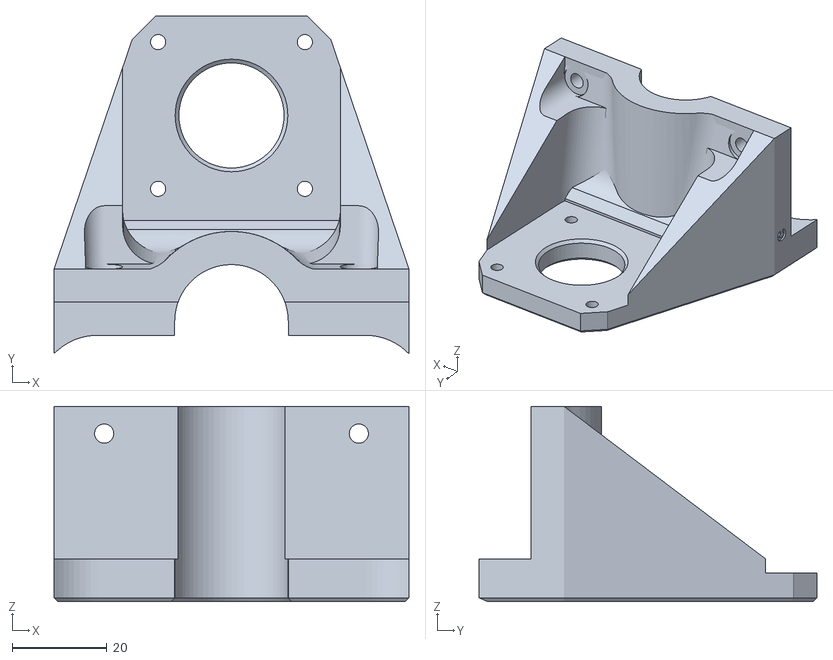
[picture p81: CAD file, 2019-01-15]
Printed_Parts/MPCNC_BURLY_C_23p5/files/C-RollerMount.STL
75.0 x 71.4 x 41.2
