mattmcwru/MPCNC-Build/Printed_Parts/MPCNC_BURLY_C_23p5/umc-projects/UM2_Bottom_Corners_x4.3mf

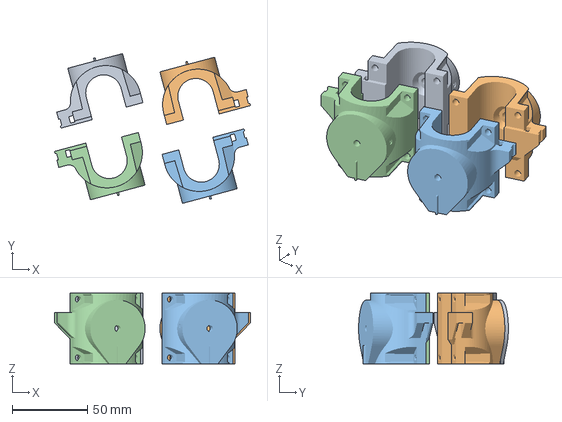
[picture p82: CAD file, 2019-01-18]
Printed_Parts/MPCNC_BURLY_C_23p5/umc-projects/UM2_Bottom_Corners_x4.3mf
130.2 x 99.5 x 47.0 mm
