mattmcwru/MPCNC-Build/Printed_Parts/MPCNC_TapeWireGuide/files/TapeWireGuide_RollerMount.stl

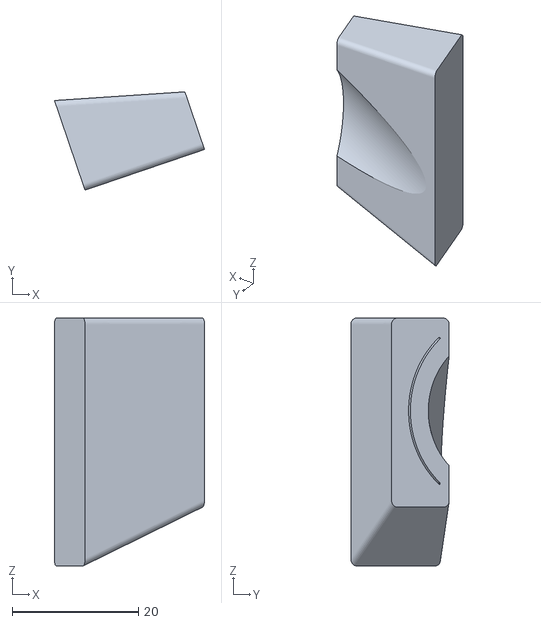
[picture p83: CAD file, 2019-02-04]
Printed_Parts/MPCNC_TapeWireGuide/files/TapeWireGuide_RollerMount.stl
23.8 x 15.6 x 39.3
