mattmcwru/MPCNC-Build/Printed_Parts/MPCNC_BURLY_C_23p5/files/Spacer_Corner_C_Burly.STL

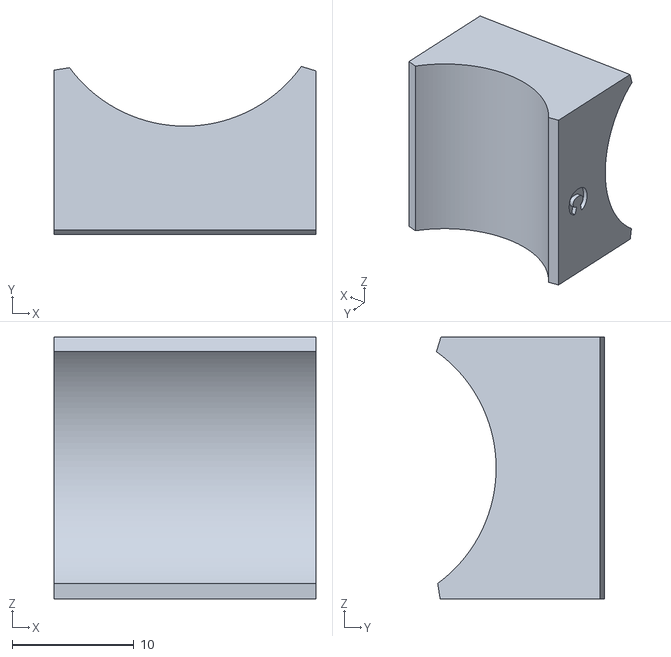
[picture p84: CAD file, 2019-01-15]
Printed_Parts/MPCNC_BURLY_C_23p5/files/Spacer_Corner_C_Burly.STL
21.5 x 13.8 x 21.5
