mattmcwru/MPCNC-Build/Printed_Parts/MPCNC_BURLY_C_23p5/umc-projects/UM2_C-Roller.3mf

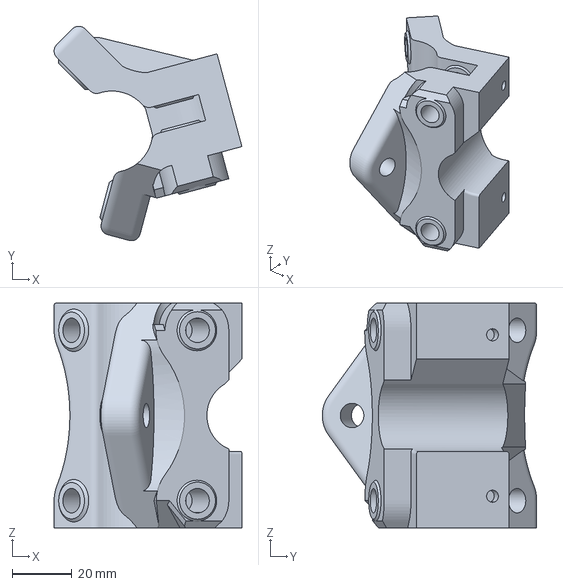
[picture p85: CAD file, 2019-01-15]
Printed_Parts/MPCNC_BURLY_C_23p5/umc-projects/UM2_C-Roller.3mf
62.6 x 71.5 x 75.0 mm
