mattmcwru/MPCNC-Build/Printed_Parts/MPCNC_BURLY_C_23p5/umc-projects/UM2_LockCornerC_x2.3mf

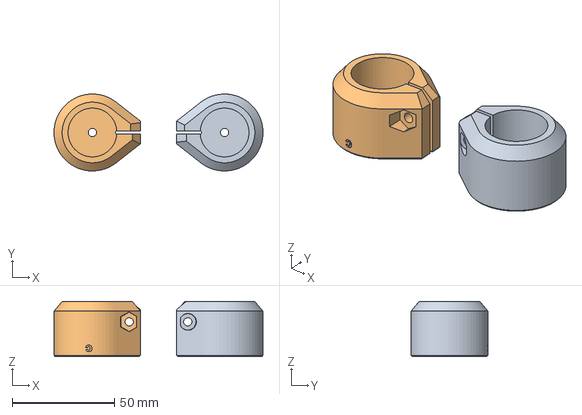
[picture p86: CAD file, 2019-01-15]
Printed_Parts/MPCNC_BURLY_C_23p5/umc-projects/UM2_LockCornerC_x2.3mf
102.3 x 37.7 x 27.0 mm
