mattmcwru/MPCNC-Build/Printed_Parts/MPCNC_BURLY_C_23p5/umc-projects/UM2_C-Foot_2018_x3.3mf

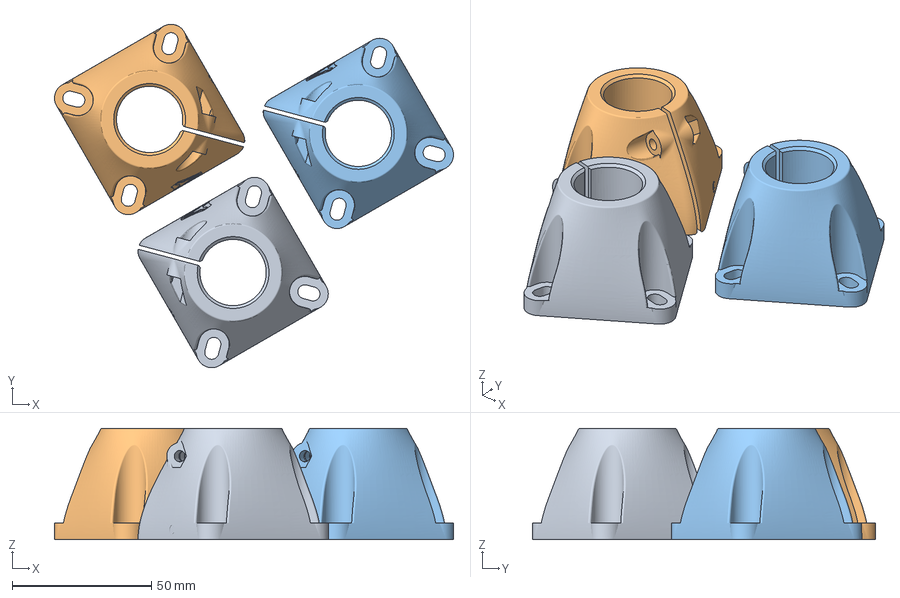
[picture p87: CAD file, 2019-01-15]
Printed_Parts/MPCNC_BURLY_C_23p5/umc-projects/UM2_C-Foot_2018_x3.3mf
143.4 x 123.4 x 40.0 mm
