mattmcwru/MPCNC-Build/Printed_Parts/MPCNC_BURLY_C_23p5/umc-projects/UM2_Gantry_Spacer_C.3mf

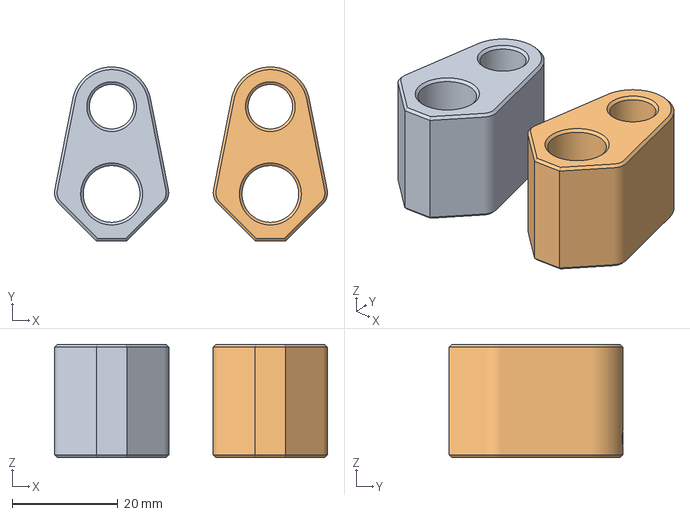
[picture p88: CAD file, 2019-01-15]
Printed_Parts/MPCNC_BURLY_C_23p5/umc-projects/UM2_Gantry_Spacer_C.3mf
51.6 x 32.9 x 21.4 mm
