mattmcwru/MPCNC-Build/Printed_Parts/MPCNC_BURLY_C_23p5/umc-projects/UM2_Bottom_CornerC_test.3mf

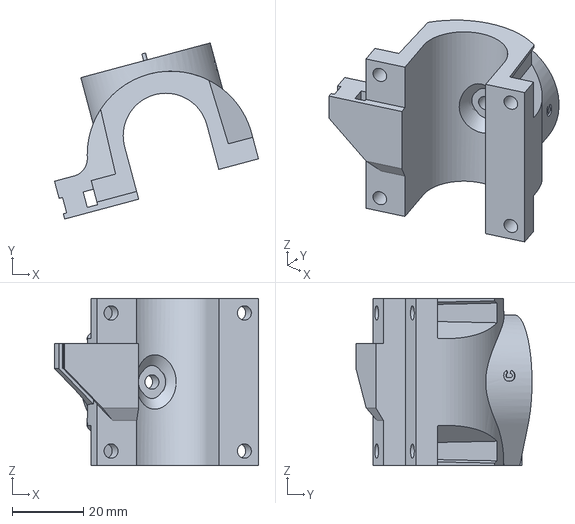
[picture p89: CAD file, 2019-01-15]
Printed_Parts/MPCNC_BURLY_C_23p5/umc-projects/UM2_Bottom_CornerC_test.3mf
57.3 x 49.5 x 47.0 mm
